koendv/arm_can_tool/Hardware/V1.0/5_3D/enclosure/README.md

3D shell for [arm_can_tool](https://oshwlab.com/koendv/arm_can_tool)

| Model | Print using | Color | Description |
| --- | --- | --- | --- |
| 3DShell_3DShell_PCB1_B.stl | SLA resin 8001 | transparent | 3D Shell, Display side |
| 3DShell_3DShell_PCB1_T.stl | SLA resin 9600 | white | 3D Shell, Component side |
