koendv/arm_can_tool/Hardware/V1.0/5_3D/fixture/README.md

 PCB Assembly Fixture for glueing ZJY154-2828KSWKG03 OLED to ARM CAN TOOL PCB.
 
 This fixture 
 
 - HOLDS the 60x100mm PCB securely in place via press-fit bumps
 - POSITIONS the OLED display accurately for gluing
