koendv/arm_can_tool/doc/pictures/3d_pcb_front.png

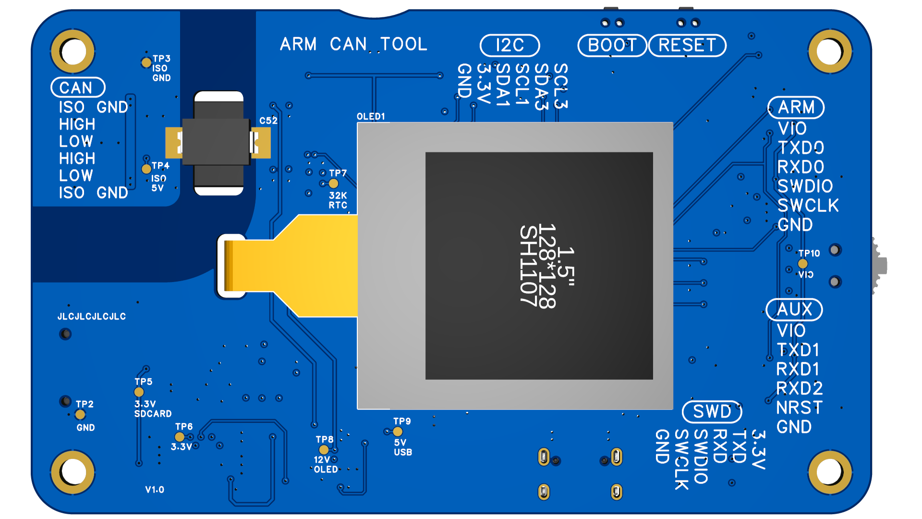
doc/pictures/3d_pcb_front.png
