koendv/arm_can_tool/doc/pictures/back_big.jpg

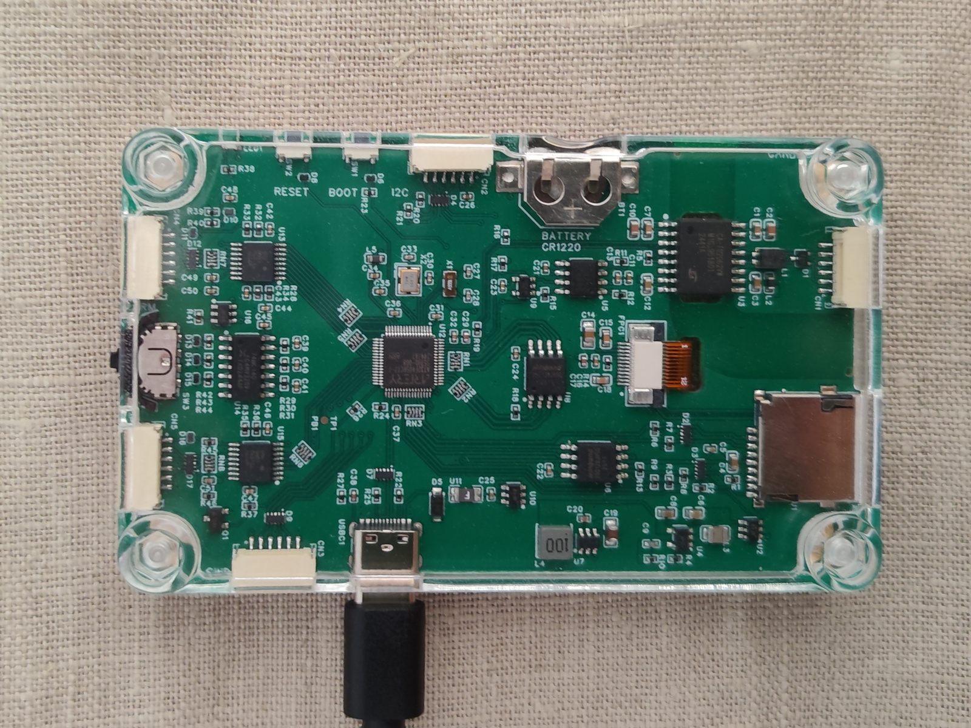
doc/pictures/back_big.jpg
