koendv/arm_can_tool/doc/pictures/handbook.png

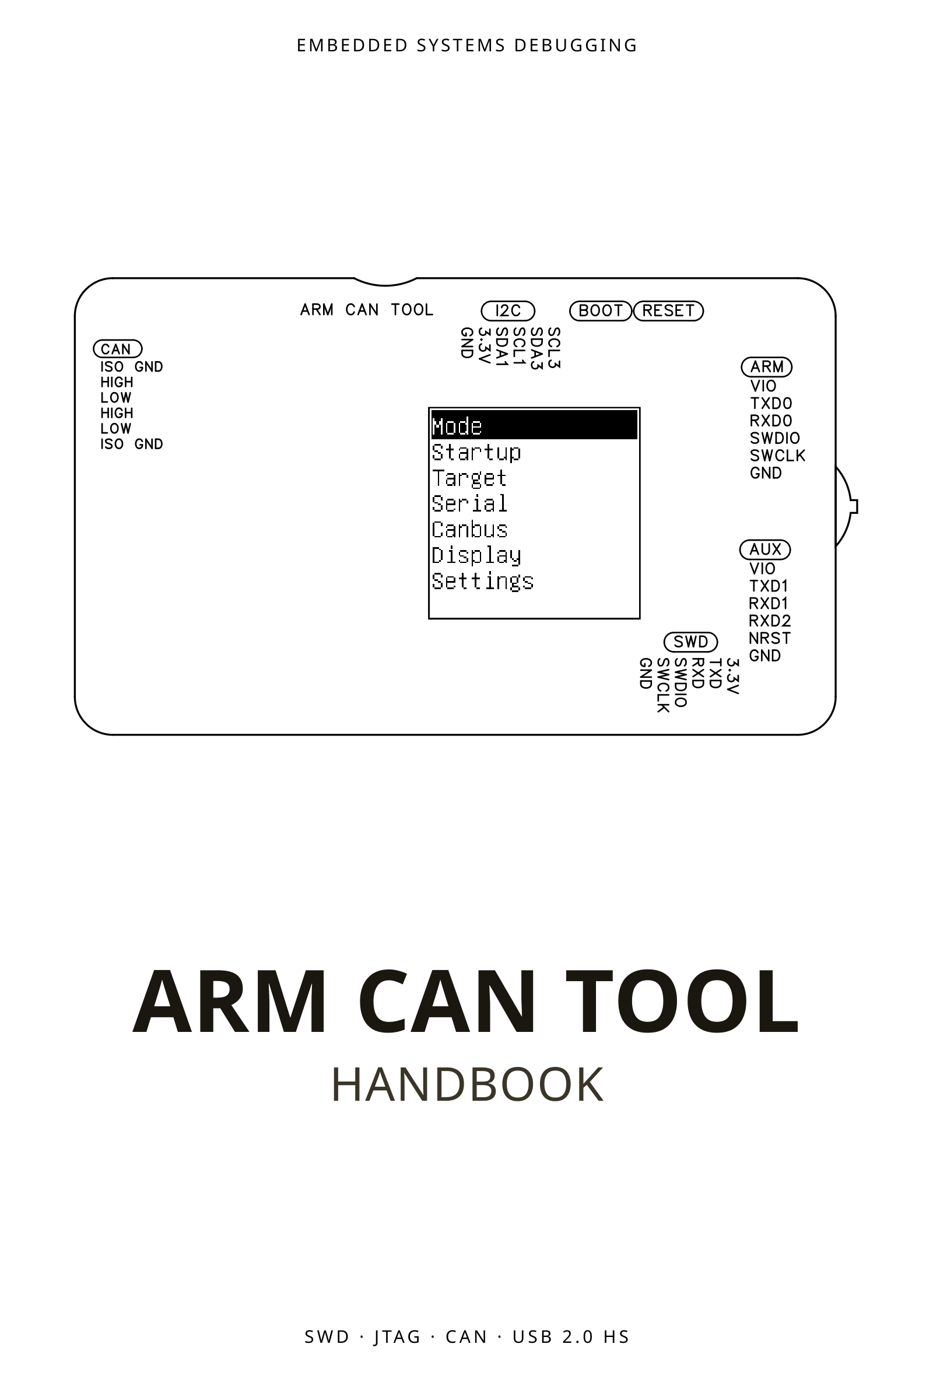
doc/pictures/handbook.png
