koendv/arm_can_tool/doc/pictures/menu_mode.png

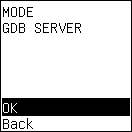
doc/pictures/menu_mode.png
