koendv/arm_can_tool/doc/pictures/oled_zjy.png

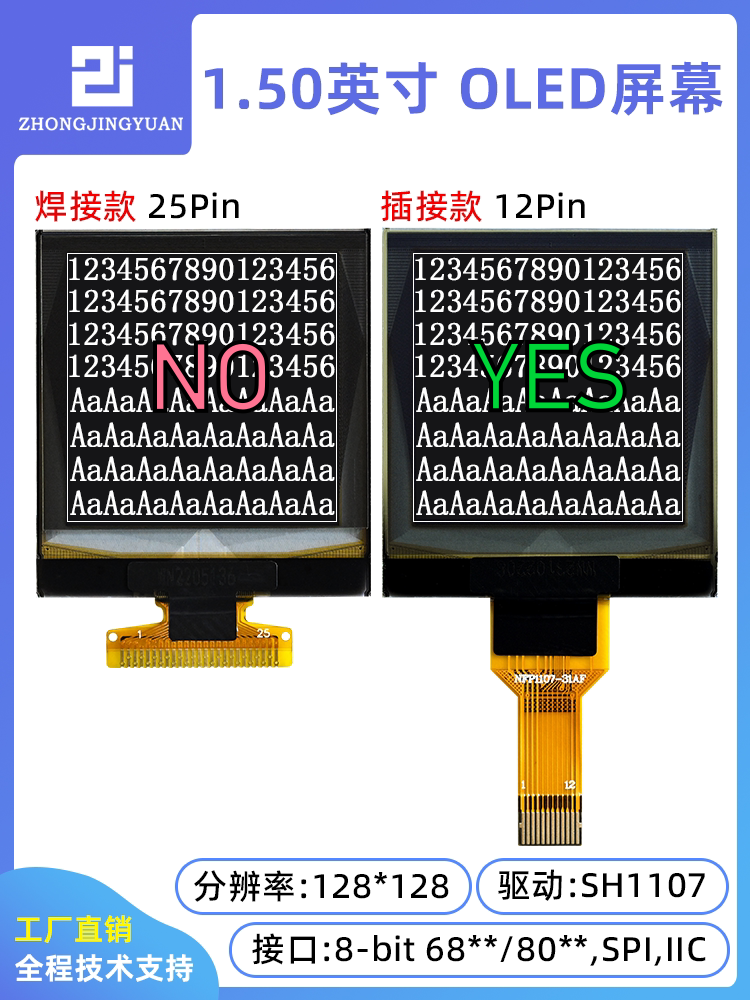
doc/pictures/oled_zjy.png
