koendv/arm_can_tool/doc/pictures/pcb_display_big.jpg

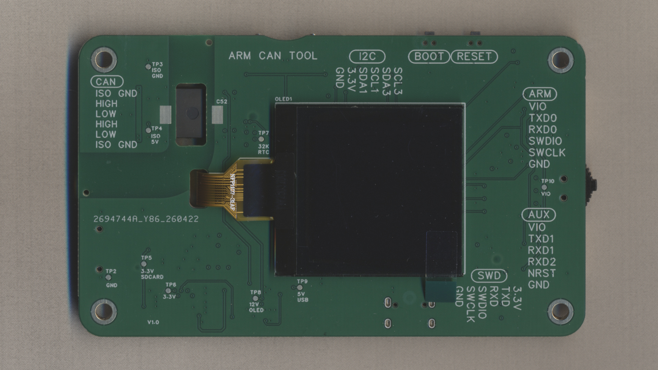
doc/pictures/pcb_display_big.jpg
