koendv/arm_can_tool/doc/pictures/target_cable.jpg

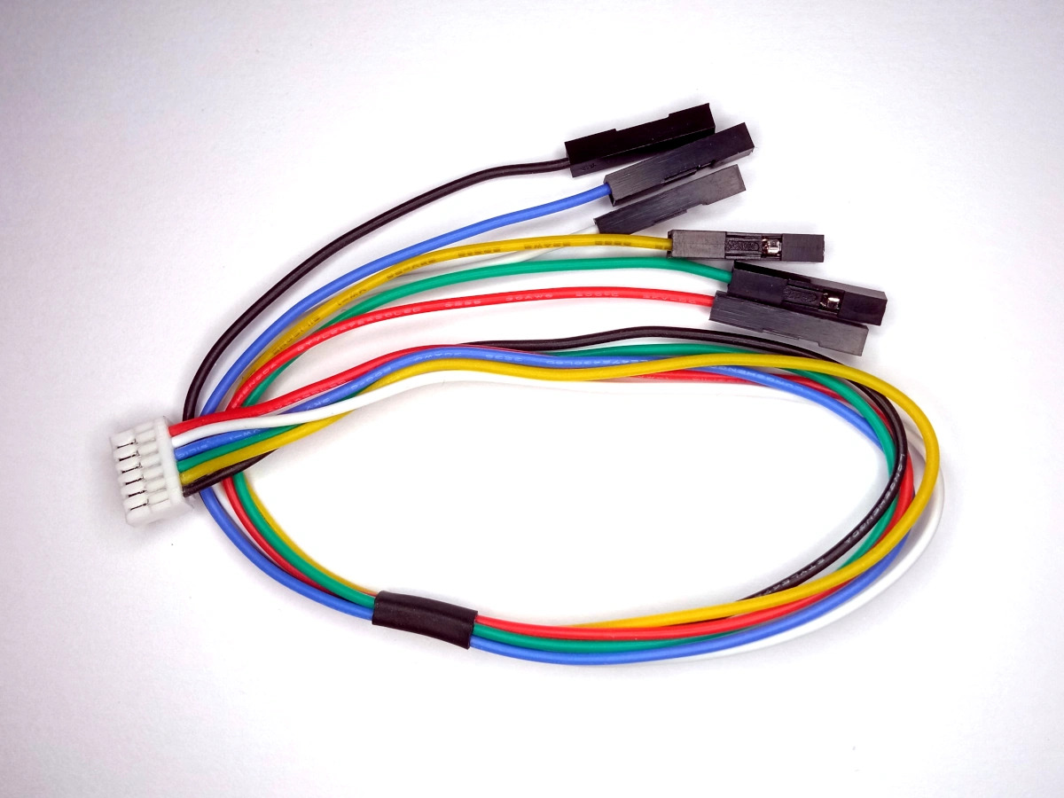
doc/pictures/target_cable.jpg
