koendv/arm_can_tool/Hardware/V1.0/6_DOC/pcb_analysis.yaml

metadata:
  component_count: 174
  net_count: 136
  verbosity_level: 5
  verbosity_description: 'EXHAUSTIVE: + All original BOM fields'
  generation_timestamp: '2026-04-23T06:47:56.703190'
  generator: EasyEDA Parser v1.0
  data_sources:
    bom: 'Bill of Materials: Component specifications, values, manufacturers'
    pickplace: 'Pick & Place: Physical coordinates, rotation, layer for assembly'
    netlist: 'Netlist: Electrical pin-to-pin connectivity'
    schematic: 'Schematic PDF: SCH_Schematic1_2026-04-18.pdf, 3 pages'
  project:
    name: arm_can_tool
    author: koendv
    license: CC0 PUBLIC DOMAIN
    version: '1.0'
    schematic_part_number: JLCPCB-002
    schematic_size: A3
    schematic_pages: 3
    schematic_create_date: '2026-01-16'
    schematic_update_date: '2026-04-17'
    page_titles:
      P1: PROCESSOR AND POWER
      P2: I2C AND SPI
      P3: TARGET AND CAN
  pcb_fab:
    vendor: JLCPCB
    stackup: JLC04161H-7628
    layers: 4
    controlled_impedance: true
    impedance_targets:
      usb_differential_pair: 90_ohm_differential
      single_ended_50ohm: 13_mil_trace
      usb_trace_spacing: 8_mil_space
      usb_trace_width: 10_mil
  design_checklist:
  - item: No silkscreen in CAN bus isolation barrier
    status: required
  - item: DS3231 RTC interrupt on MCU EXTI pin (PC13)
    status: verified
  - item: Target T_SWO/TRACESWO on USART RX
    status: verify_in_firmware
  - item: SD card length and impedance matching
    status: layout_action_required
  - item: USB differential pair length matching and 90-ohm impedance
    status: layout_action_required
  - item: Transmission lines routed over ground plane
    status: layout_action_required
  - item: No solder paste on middle pad of battery holder BT1 (C964818)
    status: assembly_note
  - item: Order number on PCB - specify position
    status: fab_action_required
  mechanical:
    shell_component_side: SLA resin 9600 white
    shell_display_side: SLA resin 8100 transparent
    fasteners: 4x nylon M3 10mm screws and nuts
    mounting_holes: M1 M2 M3 M4 (3.2mm)
  emc_notes:
  - C52 (2.2nF 400VAC Y-capacitor across isolation barrier) DNP by default, EMC debugging
    only
  - L1 ACT1210-510-2P-TL00 is a dual-winding common-mode choke on CAN_HI/CAN_LO
  - L2 GZ1608D601TF is a ferrite bead on CAN_5V_IN supply
  coordinate_system:
    units: millimeters (mm)
    origin: Bottom-left corner of PCB (standard PCB manufacturing coordinates)
    x_axis: Horizontal, increasing to the right
    y_axis: Vertical, increasing upward
    rotation: Degrees, counter-clockwise positive (0° = component oriented as in datasheet)
    placement_reference: Coordinates are from the component center (Mid X, Mid Y)
    estimated_board_size: 65.4mm × 103.1mm
    component_extent: &id001
      min_x_mm: 1.7
      max_x_mm: 57.0
      min_y_mm: 3.9
      max_y_mm: 97.0
      width_mm: 55.4
      height_mm: 93.1
  layer_codes:
    T: Top layer (components on top side of PCB)
    B: Bottom layer (components on bottom side)
  interpretation_notes:
  - Component types (R=resistor, C=capacitor, L=inductor, U=IC, etc.) are inferred
    from designator prefixes
  - Placement coordinates show physical layout - components near each other are functionally
    related
  - Net connections show electrical connectivity - components on same net are electrically
    connected
  - Rotation 0° means component oriented as shown in datasheet, 90° means rotated
    90° counter-clockwise
  - This data comes from EasyEDA Pro exports and preserves all original information
  board_dimensions:
    width_mm: 65.4
    height_mm: 103.1
    estimated_board_size: 65.4mm × 103.1mm
    component_extent: *id001
    note: Dimensions estimated from component placement with 5mm margin
components:
- designator: BT1
  type: battery
  value: MY-1220-03
  footprint: BAT-SMD_MY-1220-03
  comment: MY-1220-03
  manufacturer: MYOUNG(美阳)
  manufacturer_part: MY-1220-03
  supplier_part: C964818
  placement:
    x_mm: 5.08
    y_mm: 59.69
    rotation_deg: 90.0
    layer: T
  pins:
    '1': VBAT
    '2': VBAT
    '3': GND
  bom_data:
    No.: '1'
    Designator: BT1
    Quantity: '1'
    Manufacturer: MYOUNG(美阳)
    Manufacturer Part: MY-1220-03
    Comment: MY-1220-03
    Footprint: BAT-SMD_MY-1220-03
    Mounting Style: SMT
    Supplier Part: C964818
    Datasheet: https://atta.szlcsc.com/upload/public/pdf/source/20201218/C964818_B03812FB908E34364C1125E65C8EBE5C.pdf
  schematic_page: P1
  function_block: RTC backup battery
  schematic_notes:
  - CR1220 coin cell; powers VBAT rail when main supply is absent
  - 'Assembly: no solder paste on middle pad of holder C964818'
- designator: C1
  type: capacitor
  value: 100nF
  footprint: C0603
  comment: 100nF
  manufacturer: YAGEO(国巨)
  manufacturer_part: CC0603KRX7R9BB104
  supplier_part: C14663
  placement:
    x_mm: 12.065
    y_mm: 85.725
    rotation_deg: 180.0
    layer: T
  pins:
    '1': CAN_GND
    '2': CAN_5V_OUT
  bom_data:
    No.: '2'
    Designator: C1,C7,C15,C18
    Quantity: '4'
    Manufacturer: YAGEO(国巨)
    Manufacturer Part: CC0603KRX7R9BB104
    Comment: 100nF
    Footprint: C0603
    Mounting Style: SMT
    Supplier Part: C14663
    Datasheet: https://atta.szlcsc.com/upload/public/pdf/source/20180910/C282072_33301C7F631E79921B82A8DAC6BCC5B3.pdf
  schematic_page: P3
  function_block: CAN transceiver VCC decoupling (3.3V side)
  schematic_notes:
  - 100nF decoupling for U3 VCC pin (3.3V domain)
- designator: C2
  type: capacitor
  value: 10uF
  footprint: C0603
  comment: 10uF
  manufacturer: SAMSUNG(三星)
  manufacturer_part: CL10A106MA8NRNC
  supplier_part: C96446
  placement:
    x_mm: 12.065
    y_mm: 87.63
    rotation_deg: 180.0
    layer: T
  pins:
    '1': CAN_GND
    '2': CAN_5V_OUT
  bom_data:
    No.: '3'
    Designator: C2,C10
    Quantity: '2'
    Manufacturer: SAMSUNG(三星)
    Manufacturer Part: CL10A106MA8NRNC
    Comment: 10uF
    Footprint: C0603
    Mounting Style: SMT
    Supplier Part: C96446
    Datasheet: https://atta.szlcsc.com/upload/public/pdf/source/20160218/1457707763339.pdf
  schematic_page: P3
  function_block: CAN transceiver VCC bulk decoupling (3.3V side)
  schematic_notes:
  - 10uF bulk cap for U3 VCC (3.3V domain)
- designator: C3
  type: capacitor
  value: 1uF
  footprint: C0603
  comment: 1uF
  manufacturer: SAMSUNG(三星)
  manufacturer_part: CL10A105KB8NNNC
  supplier_part: C15849
  placement:
    x_mm: 19.304
    y_mm: 85.725
    rotation_deg: 180.0
    layer: T
  pins:
    '1': CAN_GND
    '2': CAN_5V_IN
  bom_data:
    No.: '4'
    Designator: C3,C12
    Quantity: '2'
    Manufacturer: SAMSUNG(三星)
    Manufacturer Part: CL10A105KB8NNNC
    Comment: 1uF
    Footprint: C0603
    Mounting Style: SMT
    Supplier Part: C15849
    Datasheet: https://atta.szlcsc.com/upload/public/pdf/source/20160218/1457707763339.pdf
  schematic_page: P3
  function_block: CAN transceiver VISO decoupling
  schematic_notes:
  - 1uF decoupling for U3 isolated VISO supply (CAN side)
- designator: C4
  type: capacitor
  value: 4.7uF
  footprint: C0603
  comment: 4.7uF
  manufacturer: SAMSUNG(三星)
  manufacturer_part: CL10A475KO8NNNC
  supplier_part: C19666
  placement:
    x_mm: 43.81
    y_mm: 82.677
    rotation_deg: 180.0
    layer: T
  pins:
    '1': GND
    '2': VSD
  bom_data:
    No.: '5'
    Designator: C4,C8
    Quantity: '2'
    Manufacturer: SAMSUNG(三星)
    Manufacturer Part: CL10A475KO8NNNC
    Comment: 4.7uF
    Footprint: C0603
    Mounting Style: SMT
    Supplier Part: C19666
    Datasheet: https://item.szlcsc.com/datasheet/CL10A475KO8NNNC/20375.html
  schematic_page: P2
  function_block: SD card VSD bulk decoupling
  schematic_notes:
  - 4.7uF bulk decoupling on VSD rail for SD card power switch U2
- designator: C5
  type: capacitor
  value: 100nF
  footprint: C0402
  comment: 100nF
  manufacturer: SAMSUNG(三星)
  manufacturer_part: CL05B104KO5NNNC
  supplier_part: C1525
  placement:
    x_mm: 42.037
    y_mm: 79.629
    rotation_deg: 270.0
    layer: T
  pins:
    '1': VSD
    '2': GND
  bom_data:
    No.: '6'
    Designator: C5,C13,C16,C22,C23,C24,C31,C32,C35,C36,C37,C42,C43,C44,C45,C46,C47,C48,C50,C51
    Quantity: '20'
    Manufacturer: SAMSUNG(三星)
    Manufacturer Part: CL05B104KO5NNNC
    Comment: 100nF
    Footprint: C0402
    Mounting Style: SMT
    Supplier Part: C1525
    Datasheet: https://atta.szlcsc.com/upload/public/pdf/source/20160218/1457707763339.pdf
  schematic_page: P2
  function_block: SD card VSD decoupling
  schematic_notes:
  - 100nF decoupling on VSD rail
- designator: C6
  type: capacitor
  value: 22uF
  footprint: C0603
  comment: 22uF
  manufacturer: SAMSUNG(三星)
  manufacturer_part: CL10A226MQ8NRNC
  supplier_part: C59461
  placement:
    x_mm: 50.8
    y_mm: 77.343
    rotation_deg: 90.0
    layer: T
  pins:
    '1': GND
    '2': 3.3V
  bom_data:
    No.: '7'
    Designator: C6
    Quantity: '1'
    Manufacturer: SAMSUNG(三星)
    Manufacturer Part: CL10A226MQ8NRNC
    Comment: 22uF
    Footprint: C0603
    Mounting Style: SMT
    Supplier Part: C59461
    Datasheet: https://atta.szlcsc.com/upload/public/pdf/source/20160218/1457707763339.pdf
  schematic_page: P1
  function_block: 3.3V bulk decoupling (CPU)
  schematic_notes:
  - 22uF bulk cap on 3.3V rail near MCU U12
- designator: C7
  type: capacitor
  value: 100nF
  footprint: C0603
  comment: 100nF
  manufacturer: YAGEO(国巨)
  manufacturer_part: CC0603KRX7R9BB104
  supplier_part: C14663
  placement:
    x_mm: 12.065
    y_mm: 70.739
    rotation_deg: 180.0
    layer: T
  pins:
    '1': GND
    '2': 5V
  bom_data:
    No.: '2'
    Designator: C1,C7,C15,C18
    Quantity: '4'
    Manufacturer: YAGEO(国巨)
    Manufacturer Part: CC0603KRX7R9BB104
    Comment: 100nF
    Footprint: C0603
    Mounting Style: SMT
    Supplier Part: C14663
    Datasheet: https://atta.szlcsc.com/upload/public/pdf/source/20180910/C282072_33301C7F631E79921B82A8DAC6BCC5B3.pdf
  schematic_page: P3
  function_block: CAN transceiver 5V decoupling
  schematic_notes:
  - 100nF decoupling for U3 VCC 5V supply
- designator: C8
  type: capacitor
  value: 4.7uF
  footprint: C0603
  comment: 4.7uF
  manufacturer: SAMSUNG(三星)
  manufacturer_part: CL10A475KO8NNNC
  supplier_part: C19666
  placement:
    x_mm: 50.8
    y_mm: 73.533
    rotation_deg: 270.0
    layer: T
  pins:
    '1': GND
    '2': 5V
  bom_data:
    No.: '5'
    Designator: C4,C8
    Quantity: '2'
    Manufacturer: SAMSUNG(三星)
    Manufacturer Part: CL10A475KO8NNNC
    Comment: 4.7uF
    Footprint: C0603
    Mounting Style: SMT
    Supplier Part: C19666
    Datasheet: https://item.szlcsc.com/datasheet/CL10A475KO8NNNC/20375.html
  schematic_page: P1
  function_block: USB VBUS bulk decoupling
  schematic_notes:
  - 4.7uF bulk decoupling on 5V/VBUS rail near USB-C connector
- designator: C9
  type: capacitor
  value: 22pF
  footprint: C0402
  comment: 22pF
  manufacturer: FH(风华)
  manufacturer_part: 0402CG220J500NT
  supplier_part: C1555
  placement:
    x_mm: 54.991
    y_mm: 71.501
    rotation_deg: 270.0
    layer: T
  pins:
    '1': VFB
    '2': 3.3V
  bom_data:
    No.: '8'
    Designator: C9
    Quantity: '1'
    Manufacturer: FH(风华)
    Manufacturer Part: 0402CG220J500NT
    Comment: 22pF
    Footprint: C0402
    Mounting Style: SMT
    Supplier Part: C1555
  schematic_page: P1
  function_block: Buck converter VFB feed-forward capacitor
  schematic_notes:
  - 22pF feed-forward cap across upper feedback resistor R10 for TLV62569 U4
  - Improves phase margin of 3.3V buck converter loop
- designator: C10
  type: capacitor
  value: 10uF
  footprint: C0603
  comment: 10uF
  manufacturer: SAMSUNG(三星)
  manufacturer_part: CL10A106MA8NRNC
  supplier_part: C96446
  placement:
    x_mm: 12.065
    y_mm: 68.834
    rotation_deg: 180.0
    layer: T
  pins:
    '1': GND
    '2': 5V
  bom_data:
    No.: '3'
    Designator: C2,C10
    Quantity: '2'
    Manufacturer: SAMSUNG(三星)
    Manufacturer Part: CL10A106MA8NRNC
    Comment: 10uF
    Footprint: C0603
    Mounting Style: SMT
    Supplier Part: C96446
    Datasheet: https://atta.szlcsc.com/upload/public/pdf/source/20160218/1457707763339.pdf
  schematic_page: P3
  function_block: CAN transceiver VISO bulk decoupling
  schematic_notes:
  - 10uF bulk cap on U3 isolated VISO rail (CAN side)
- designator: C11
  type: capacitor
  value: 1uF
  footprint: C0402
  comment: 1uF
  manufacturer: SAMSUNG(三星)
  manufacturer_part: CL05A105KA5NQNC
  supplier_part: C52923
  placement:
    x_mm: 18.796
    y_mm: 68.199
    rotation_deg: 0.0
    layer: T
  pins:
    '1': GND
    '2': 3.3V
  bom_data:
    No.: '9'
    Designator: C11,C21,C25,C26,C34,C39,C40,C41,C49
    Quantity: '9'
    Manufacturer: SAMSUNG(三星)
    Manufacturer Part: CL05A105KA5NQNC
    Comment: 1uF
    Footprint: C0402
    Mounting Style: SMT
    Supplier Part: C52923
    Datasheet: https://atta.szlcsc.com/upload/public/pdf/source/20160218/1457707763339.pdf
  schematic_page: P2
  function_block: 3.3V decoupling (I2C/SPI area)
  schematic_notes:
  - 1uF local 3.3V decoupling near I2C/SPI peripherals
- designator: C12
  type: capacitor
  value: 1uF
  footprint: C0603
  comment: 1uF
  manufacturer: SAMSUNG(三星)
  manufacturer_part: CL10A105KB8NNNC
  supplier_part: C15849
  placement:
    x_mm: 19.685
    y_mm: 70.739
    rotation_deg: 180.0
    layer: T
  pins:
    '1': GND
    '2': 3.3V
  bom_data:
    No.: '4'
    Designator: C3,C12
    Quantity: '2'
    Manufacturer: SAMSUNG(三星)
    Manufacturer Part: CL10A105KB8NNNC
    Comment: 1uF
    Footprint: C0603
    Mounting Style: SMT
    Supplier Part: C15849
    Datasheet: https://atta.szlcsc.com/upload/public/pdf/source/20160218/1457707763339.pdf
  schematic_page: P3
  function_block: CAN transceiver VISO decoupling
  schematic_notes:
  - 1uF decoupling on U3 isolated VISO supply
- designator: C13
  type: capacitor
  value: 100nF
  footprint: C0402
  comment: 100nF
  manufacturer: SAMSUNG(三星)
  manufacturer_part: CL05B104KO5NNNC
  supplier_part: C1525
  placement:
    x_mm: 18.796
    y_mm: 66.675
    rotation_deg: 0.0
    layer: T
  pins:
    '1': GND
    '2': 3.3V
  bom_data:
    No.: '6'
    Designator: C5,C13,C16,C22,C23,C24,C31,C32,C35,C36,C37,C42,C43,C44,C45,C46,C47,C48,C50,C51
    Quantity: '20'
    Manufacturer: SAMSUNG(三星)
    Manufacturer Part: CL05B104KO5NNNC
    Comment: 100nF
    Footprint: C0402
    Mounting Style: SMT
    Supplier Part: C1525
    Datasheet: https://atta.szlcsc.com/upload/public/pdf/source/20160218/1457707763339.pdf
  schematic_page: P2
  function_block: RTC 3.3V decoupling
  schematic_notes:
  - 100nF decoupling for RTC IC U5
- designator: C14
  type: capacitor
  value: 2.2uF
  footprint: C0805
  comment: 2.2uF
  manufacturer: SAMSUNG(三星)
  manufacturer_part: CL21A225KBQNNNE
  supplier_part: C377773
  placement:
    x_mm: 26.543
    y_mm: 62.738
    rotation_deg: 0.0
    layer: T
  pins:
    '1': GND
    '2': VCOMH
  bom_data:
    No.: '10'
    Designator: C14
    Quantity: '1'
    Manufacturer: SAMSUNG(三星)
    Manufacturer Part: CL21A225KBQNNNE
    Comment: 2.2uF
    Footprint: C0805
    Mounting Style: SMT
    Supplier Part: C377773
    Datasheet: https://atta.szlcsc.com/upload/public/pdf/source/20160218/1457707763339.pdf
  schematic_page: P2
  function_block: Display VCOMH storage capacitor
  schematic_notes:
  - 2.2uF VCOMH cap for OLED display via FPC1
  - 50V rated for 12V supply domain
- designator: C15
  type: capacitor
  value: 100nF
  footprint: C0603
  comment: 100nF
  manufacturer: YAGEO(国巨)
  manufacturer_part: CC0603KRX7R9BB104
  supplier_part: C14663
  placement:
    x_mm: 27.051
    y_mm: 65.151
    rotation_deg: 0.0
    layer: T
  pins:
    '1': GND
    '2': 12V
  bom_data:
    No.: '2'
    Designator: C1,C7,C15,C18
    Quantity: '4'
    Manufacturer: YAGEO(国巨)
    Manufacturer Part: CC0603KRX7R9BB104
    Comment: 100nF
    Footprint: C0603
    Mounting Style: SMT
    Supplier Part: C14663
    Datasheet: https://atta.szlcsc.com/upload/public/pdf/source/20180910/C282072_33301C7F631E79921B82A8DAC6BCC5B3.pdf
  schematic_page: P2
  function_block: 12V boost output decoupling
  schematic_notes:
  - 100nF output decoupling for 12V boost U7; 50V rated
- designator: C16
  type: capacitor
  value: 100nF
  footprint: C0402
  comment: 100nF
  manufacturer: SAMSUNG(三星)
  manufacturer_part: CL05B104KO5NNNC
  supplier_part: C1525
  placement:
    x_mm: 30.226
    y_mm: 63.754
    rotation_deg: 180.0
    layer: T
  pins:
    '1': GND
    '2': 3.3V
  bom_data:
    No.: '6'
    Designator: C5,C13,C16,C22,C23,C24,C31,C32,C35,C36,C37,C42,C43,C44,C45,C46,C47,C48,C50,C51
    Quantity: '20'
    Manufacturer: SAMSUNG(三星)
    Manufacturer Part: CL05B104KO5NNNC
    Comment: 100nF
    Footprint: C0402
    Mounting Style: SMT
    Supplier Part: C1525
    Datasheet: https://atta.szlcsc.com/upload/public/pdf/source/20160218/1457707763339.pdf
  schematic_page: P2
  function_block: 12V domain decoupling
  schematic_notes:
  - 100nF decoupling on 12V rail near display FPC1
- designator: C17
  type: capacitor
  value: 4.7uF
  footprint: C0402
  comment: 4.7uF
  manufacturer: SAMSUNG(三星)
  manufacturer_part: CL05A475MP5NRNC
  supplier_part: C23733
  placement:
    x_mm: 30.226
    y_mm: 62.103
    rotation_deg: 180.0
    layer: T
  pins:
    '1': GND
    '2': 3.3V
  bom_data:
    No.: '11'
    Designator: C17,C20,C29
    Quantity: '3'
    Manufacturer: SAMSUNG(三星)
    Manufacturer Part: CL05A475MP5NRNC
    Comment: 4.7uF
    Footprint: C0402
    Mounting Style: SMT
    Supplier Part: C23733
    Datasheet: https://atta.szlcsc.com/upload/public/pdf/source/20160218/1457707763339.pdf
  schematic_page: P2
  function_block: 12V domain bulk decoupling
  schematic_notes:
  - 4.7uF bulk decoupling on 12V rail near display FPC1
- designator: C18
  type: capacitor
  value: 100nF
  footprint: C0603
  comment: 100nF
  manufacturer: YAGEO(国巨)
  manufacturer_part: CC0603KRX7R9BB104
  supplier_part: C14663
  placement:
    x_mm: 32.766
    y_mm: 64.516
    rotation_deg: 90.0
    layer: T
  pins:
    '1': GND
    '2': 12V
  bom_data:
    No.: '2'
    Designator: C1,C7,C15,C18
    Quantity: '4'
    Manufacturer: YAGEO(国巨)
    Manufacturer Part: CC0603KRX7R9BB104
    Comment: 100nF
    Footprint: C0603
    Mounting Style: SMT
    Supplier Part: C14663
    Datasheet: https://atta.szlcsc.com/upload/public/pdf/source/20180910/C282072_33301C7F631E79921B82A8DAC6BCC5B3.pdf
  schematic_page: P2
  function_block: 12V boost output decoupling
  schematic_notes:
  - 100nF output decoupling for U7 12V boost; 50V rated
- designator: C19
  type: capacitor
  value: 10uF
  footprint: C0805
  comment: 10uF
  manufacturer: muRata(村田)
  manufacturer_part: GRM21BR61H106KE43L
  supplier_part: C440198
  placement:
    x_mm: 53.467
    y_mm: 65.913
    rotation_deg: 180.0
    layer: T
  pins:
    '1': GND
    '2': 12V
  bom_data:
    No.: '12'
    Designator: C19
    Quantity: '1'
    Manufacturer: muRata(村田)
    Manufacturer Part: GRM21BR61H106KE43L
    Comment: 10uF
    Footprint: C0805
    Mounting Style: SMT
    Supplier Part: C440198
    Datasheet: https://atta.szlcsc.com/upload/public/pdf/source/20230811/95AAE0C9AF55EDC31B7A4D8B733F534E.pdf
  schematic_page: P2
  function_block: 12V boost output bulk capacitor
  schematic_notes:
  - 10uF bulk output cap for 12V boost U7; 50V rated (Murata)
- designator: C20
  type: capacitor
  value: 4.7uF
  footprint: C0402
  comment: 4.7uF
  manufacturer: SAMSUNG(三星)
  manufacturer_part: CL05A475MP5NRNC
  supplier_part: C23733
  placement:
    x_mm: 51.562
    y_mm: 62.23
    rotation_deg: 270.0
    layer: T
  pins:
    '1': GND
    '2': 5V
  bom_data:
    No.: '11'
    Designator: C17,C20,C29
    Quantity: '3'
    Manufacturer: SAMSUNG(三星)
    Manufacturer Part: CL05A475MP5NRNC
    Comment: 4.7uF
    Footprint: C0402
    Mounting Style: SMT
    Supplier Part: C23733
    Datasheet: https://atta.szlcsc.com/upload/public/pdf/source/20160218/1457707763339.pdf
  schematic_page: P2
  function_block: 5V decoupling (boost converter input)
  schematic_notes:
  - 4.7uF input decoupling for 12V boost U7, on 5V rail
- designator: C21
  type: capacitor
  value: 1uF
  footprint: C0402
  comment: 1uF
  manufacturer: SAMSUNG(三星)
  manufacturer_part: CL05A105KA5NQNC
  supplier_part: C52923
  placement:
    x_mm: 17.526
    y_mm: 56.769
    rotation_deg: 0.0
    layer: T
  pins:
    '1': GND
    '2': VBAT
  bom_data:
    No.: '9'
    Designator: C11,C21,C25,C26,C34,C39,C40,C41,C49
    Quantity: '9'
    Manufacturer: SAMSUNG(三星)
    Manufacturer Part: CL05A105KA5NQNC
    Comment: 1uF
    Footprint: C0402
    Mounting Style: SMT
    Supplier Part: C52923
    Datasheet: https://atta.szlcsc.com/upload/public/pdf/source/20160218/1457707763339.pdf
  schematic_page: P2
  function_block: VBAT decoupling
  schematic_notes:
  - 1uF decoupling on VBAT rail for RTC backup battery BT1
- designator: C22
  type: capacitor
  value: 100nF
  footprint: C0402
  comment: 100nF
  manufacturer: SAMSUNG(三星)
  manufacturer_part: CL05B104KO5NNNC
  supplier_part: C1525
  placement:
    x_mm: 45.085
    y_mm: 57.404
    rotation_deg: 180.0
    layer: T
  pins:
    '1': 3.3V
    '2': GND
  bom_data:
    No.: '6'
    Designator: C5,C13,C16,C22,C23,C24,C31,C32,C35,C36,C37,C42,C43,C44,C45,C46,C47,C48,C50,C51
    Quantity: '20'
    Manufacturer: SAMSUNG(三星)
    Manufacturer Part: CL05B104KO5NNNC
    Comment: 100nF
    Footprint: C0402
    Mounting Style: SMT
    Supplier Part: C1525
    Datasheet: https://atta.szlcsc.com/upload/public/pdf/source/20160218/1457707763339.pdf
  schematic_page: P3
  function_block: VIO decoupling (target interface)
  schematic_notes:
  - 100nF decoupling on VIO rail for target voltage domain
- designator: C23
  type: capacitor
  value: 100nF
  footprint: C0402
  comment: 100nF
  manufacturer: SAMSUNG(三星)
  manufacturer_part: CL05B104KO5NNNC
  supplier_part: C1525
  placement:
    x_mm: 20.066
    y_mm: 50.927
    rotation_deg: 180.0
    layer: T
  pins:
    '1': GND
    '2': 3.3V
  bom_data:
    No.: '6'
    Designator: C5,C13,C16,C22,C23,C24,C31,C32,C35,C36,C37,C42,C43,C44,C45,C46,C47,C48,C50,C51
    Quantity: '20'
    Manufacturer: SAMSUNG(三星)
    Manufacturer Part: CL05B104KO5NNNC
    Comment: 100nF
    Footprint: C0402
    Mounting Style: SMT
    Supplier Part: C1525
    Datasheet: https://atta.szlcsc.com/upload/public/pdf/source/20160218/1457707763339.pdf
  schematic_page: P2
  function_block: EEPROM 3.3V decoupling
  schematic_notes:
  - 100nF decoupling for EEPROM U9
- designator: C24
  type: capacitor
  value: 100nF
  footprint: C0402
  comment: 100nF
  manufacturer: SAMSUNG(三星)
  manufacturer_part: CL05B104KO5NNNC
  supplier_part: C1525
  placement:
    x_mm: 29.286
    y_mm: 52.832
    rotation_deg: 0.0
    layer: T
  pins:
    '1': 3.3V
    '2': GND
  bom_data:
    No.: '6'
    Designator: C5,C13,C16,C22,C23,C24,C31,C32,C35,C36,C37,C42,C43,C44,C45,C46,C47,C48,C50,C51
    Quantity: '20'
    Manufacturer: SAMSUNG(三星)
    Manufacturer Part: CL05B104KO5NNNC
    Comment: 100nF
    Footprint: C0402
    Mounting Style: SMT
    Supplier Part: C1525
    Datasheet: https://atta.szlcsc.com/upload/public/pdf/source/20160218/1457707763339.pdf
  schematic_page: P1
  function_block: QSPI flash 3.3V decoupling
  schematic_notes:
  - 100nF decoupling for QSPI flash U8
- designator: C25
  type: capacitor
  value: 1uF
  footprint: C0402
  comment: 1uF
  manufacturer: SAMSUNG(三星)
  manufacturer_part: CL05A105KA5NQNC
  supplier_part: C52923
  placement:
    x_mm: 48.387
    y_mm: 49.53
    rotation_deg: 0.0
    layer: T
  pins:
    '1': GND
    '2': VBUS
  bom_data:
    No.: '9'
    Designator: C11,C21,C25,C26,C34,C39,C40,C41,C49
    Quantity: '9'
    Manufacturer: SAMSUNG(三星)
    Manufacturer Part: CL05A105KA5NQNC
    Comment: 1uF
    Footprint: C0402
    Mounting Style: SMT
    Supplier Part: C52923
    Datasheet: https://atta.szlcsc.com/upload/public/pdf/source/20160218/1457707763339.pdf
  schematic_page: P1
  function_block: USB VBUS decoupling
  schematic_notes:
  - 1uF decoupling on VBUS rail; 25V rated
- designator: C26
  type: capacitor
  value: 1uF
  footprint: C0402
  comment: 1uF
  manufacturer: SAMSUNG(三星)
  manufacturer_part: CL05A105KA5NQNC
  supplier_part: C52923
  placement:
    x_mm: 7.874
    y_mm: 45.974
    rotation_deg: 270.0
    layer: T
  pins:
    '1': GND
    '2': 3.3V
  bom_data:
    No.: '9'
    Designator: C11,C21,C25,C26,C34,C39,C40,C41,C49
    Quantity: '9'
    Manufacturer: SAMSUNG(三星)
    Manufacturer Part: CL05A105KA5NQNC
    Comment: 1uF
    Footprint: C0402
    Mounting Style: SMT
    Supplier Part: C52923
    Datasheet: https://atta.szlcsc.com/upload/public/pdf/source/20160218/1457707763339.pdf
  schematic_page: P2
  function_block: 3.3V decoupling (SPI flash area)
  schematic_notes:
  - 1uF local decoupling near SPI flash U6
- designator: C27
  type: capacitor
  value: 18pF
  footprint: C0402
  comment: 18pF
  manufacturer: FH(风华)
  manufacturer_part: 0402CG180J500NT
  supplier_part: C1549
  placement:
    x_mm: 18.161
    y_mm: 46.228
    rotation_deg: 180.0
    layer: T
  pins:
    '1': GND
    '2': OSC32_OUT
  bom_data:
    No.: '13'
    Designator: C27,C28
    Quantity: '2'
    Manufacturer: FH(风华)
    Manufacturer Part: 0402CG180J500NT
    Comment: 18pF
    Footprint: C0402
    Mounting Style: SMT
    Supplier Part: C1549
    Datasheet: https://atta.szlcsc.com/upload/public/pdf/source/20200305/C486355_26A10D38EF8C2A5C37091D0039909270.pdf
  schematic_page: P1
  function_block: RTC crystal load capacitor (OSC32_OUT)
  schematic_notes:
  - 18pF load cap for 32.768kHz crystal X1, OSC32_OUT pin
- designator: C28
  type: capacitor
  value: 18pF
  footprint: C0402
  comment: 18pF
  manufacturer: FH(风华)
  manufacturer_part: 0402CG180J500NT
  supplier_part: C1549
  placement:
    x_mm: 21.463
    y_mm: 46.228
    rotation_deg: 0.0
    layer: T
  pins:
    '1': GND
    '2': OSC32_IN
  bom_data:
    No.: '13'
    Designator: C27,C28
    Quantity: '2'
    Manufacturer: FH(风华)
    Manufacturer Part: 0402CG180J500NT
    Comment: 18pF
    Footprint: C0402
    Mounting Style: SMT
    Supplier Part: C1549
    Datasheet: https://atta.szlcsc.com/upload/public/pdf/source/20200305/C486355_26A10D38EF8C2A5C37091D0039909270.pdf
  schematic_page: P1
  function_block: RTC crystal load capacitor (OSC32_IN)
  schematic_notes:
  - 18pF load cap for 32.768kHz crystal X1, OSC32_IN pin
- designator: C29
  type: capacitor
  value: 4.7uF
  footprint: C0402
  comment: 4.7uF
  manufacturer: SAMSUNG(三星)
  manufacturer_part: CL05A475MP5NRNC
  supplier_part: C23733
  placement:
    x_mm: 27.051
    y_mm: 45.974
    rotation_deg: 180.0
    layer: T
  pins:
    '1': GND
    '2': 3.3V
  bom_data:
    No.: '11'
    Designator: C17,C20,C29
    Quantity: '3'
    Manufacturer: SAMSUNG(三星)
    Manufacturer Part: CL05A475MP5NRNC
    Comment: 4.7uF
    Footprint: C0402
    Mounting Style: SMT
    Supplier Part: C23733
    Datasheet: https://atta.szlcsc.com/upload/public/pdf/source/20160218/1457707763339.pdf
  schematic_page: P1
  function_block: 3.3V bulk decoupling (CPU)
  schematic_notes:
  - 4.7uF bulk decoupling on 3.3V rail near MCU
- designator: C30
  type: capacitor
  value: 15pF
  footprint: C0402
  comment: 15pF
  manufacturer: FH(风华)
  manufacturer_part: 0402CG150J500NT
  supplier_part: C1548
  placement:
    x_mm: 19.05
    y_mm: 40.894
    rotation_deg: 180.0
    layer: T
  pins:
    '1': OSC_IN
    '2': GND
  bom_data:
    No.: '14'
    Designator: C30,C33
    Quantity: '2'
    Manufacturer: FH(风华)
    Manufacturer Part: 0402CG150J500NT
    Comment: 15pF
    Footprint: C0402
    Mounting Style: SMT
    Supplier Part: C1548
    Datasheet: https://atta.szlcsc.com/upload/public/pdf/source/20200305/C486355_26A10D38EF8C2A5C37091D0039909270.pdf
  schematic_page: P1
  function_block: HSE crystal load capacitor (OSC_IN)
  schematic_notes:
  - 15pF load cap for 12MHz crystal X2, OSC_IN pin
  - 15pF chosen to target 12pF crystal spec with PCB stray capacitance
- designator: C31
  type: capacitor
  value: 100nF
  footprint: C0402
  comment: 100nF
  manufacturer: SAMSUNG(三星)
  manufacturer_part: CL05B104KO5NNNC
  supplier_part: C1525
  placement:
    x_mm: 24.257
    y_mm: 41.91
    rotation_deg: 270.0
    layer: T
  pins:
    '1': GND
    '2': 3.3V
  bom_data:
    No.: '6'
    Designator: C5,C13,C16,C22,C23,C24,C31,C32,C35,C36,C37,C42,C43,C44,C45,C46,C47,C48,C50,C51
    Quantity: '20'
    Manufacturer: SAMSUNG(三星)
    Manufacturer Part: CL05B104KO5NNNC
    Comment: 100nF
    Footprint: C0402
    Mounting Style: SMT
    Supplier Part: C1525
    Datasheet: https://atta.szlcsc.com/upload/public/pdf/source/20160218/1457707763339.pdf
  schematic_page: P1
  function_block: 3.3V decoupling (CPU)
  schematic_notes:
  - 100nF decoupling on 3.3V rail near MCU U12
- designator: C32
  type: capacitor
  value: 100nF
  footprint: C0402
  comment: 100nF
  manufacturer: SAMSUNG(三星)
  manufacturer_part: CL05B104KO5NNNC
  supplier_part: C1525
  placement:
    x_mm: 27.051
    y_mm: 44.323
    rotation_deg: 180.0
    layer: T
  pins:
    '1': GND
    '2': 3.3V
  bom_data:
    No.: '6'
    Designator: C5,C13,C16,C22,C23,C24,C31,C32,C35,C36,C37,C42,C43,C44,C45,C46,C47,C48,C50,C51
    Quantity: '20'
    Manufacturer: SAMSUNG(三星)
    Manufacturer Part: CL05B104KO5NNNC
    Comment: 100nF
    Footprint: C0402
    Mounting Style: SMT
    Supplier Part: C1525
    Datasheet: https://atta.szlcsc.com/upload/public/pdf/source/20160218/1457707763339.pdf
  schematic_page: P1
  function_block: BOOT0 noise filter
  schematic_notes:
  - 100nF noise filter on BOOT0 net
- designator: C33
  type: capacitor
  value: 15pF
  footprint: C0402
  comment: 15pF
  manufacturer: FH(风华)
  manufacturer_part: 0402CG150J500NT
  supplier_part: C1548
  placement:
    x_mm: 16.256
    y_mm: 38.1
    rotation_deg: 270.0
    layer: T
  pins:
    '1': GND
    '2': OSC_OUT
  bom_data:
    No.: '14'
    Designator: C30,C33
    Quantity: '2'
    Manufacturer: FH(风华)
    Manufacturer Part: 0402CG150J500NT
    Comment: 15pF
    Footprint: C0402
    Mounting Style: SMT
    Supplier Part: C1548
    Datasheet: https://atta.szlcsc.com/upload/public/pdf/source/20200305/C486355_26A10D38EF8C2A5C37091D0039909270.pdf
  schematic_page: P1
  function_block: HSE crystal load capacitor (OSC_OUT)
  schematic_notes:
  - 15pF load cap for 12MHz crystal X2, OSC_OUT pin
  - 15pF chosen to target 12pF crystal spec with PCB stray capacitance
- designator: C34
  type: capacitor
  value: 1uF
  footprint: C0402
  comment: 1uF
  manufacturer: SAMSUNG(三星)
  manufacturer_part: CL05A105KA5NQNC
  supplier_part: C52923
  placement:
    x_mm: 18.796
    y_mm: 33.401
    rotation_deg: 270.0
    layer: T
  pins:
    '1': GND
    '2': 3.3V_ANA
  bom_data:
    No.: '9'
    Designator: C11,C21,C25,C26,C34,C39,C40,C41,C49
    Quantity: '9'
    Manufacturer: SAMSUNG(三星)
    Manufacturer Part: CL05A105KA5NQNC
    Comment: 1uF
    Footprint: C0402
    Mounting Style: SMT
    Supplier Part: C52923
    Datasheet: https://atta.szlcsc.com/upload/public/pdf/source/20160218/1457707763339.pdf
  schematic_page: P1
  function_block: MCU VDDA decoupling
  schematic_notes:
  - 1uF decoupling on VDDA (analog supply) for MCU U12
- designator: C35
  type: capacitor
  value: 100nF
  footprint: C0402
  comment: 100nF
  manufacturer: SAMSUNG(三星)
  manufacturer_part: CL05B104KO5NNNC
  supplier_part: C1525
  placement:
    x_mm: 20.955
    y_mm: 34.163
    rotation_deg: 90.0
    layer: T
  pins:
    '1': GND
    '2': RST
  bom_data:
    No.: '6'
    Designator: C5,C13,C16,C22,C23,C24,C31,C32,C35,C36,C37,C42,C43,C44,C45,C46,C47,C48,C50,C51
    Quantity: '20'
    Manufacturer: SAMSUNG(三星)
    Manufacturer Part: CL05B104KO5NNNC
    Comment: 100nF
    Footprint: C0402
    Mounting Style: SMT
    Supplier Part: C1525
    Datasheet: https://atta.szlcsc.com/upload/public/pdf/source/20160218/1457707763339.pdf
  schematic_page: P1
  function_block: NRST noise filter
  schematic_notes:
  - 100nF filter cap on NRST/RST line for noise immunity
- designator: C36
  type: capacitor
  value: 100nF
  footprint: C0402
  comment: 100nF
  manufacturer: SAMSUNG(三星)
  manufacturer_part: CL05B104KO5NNNC
  supplier_part: C1525
  placement:
    x_mm: 23.876
    y_mm: 36.195
    rotation_deg: 270.0
    layer: T
  pins:
    '1': GND
    '2': 3.3V_ANA
  bom_data:
    No.: '6'
    Designator: C5,C13,C16,C22,C23,C24,C31,C32,C35,C36,C37,C42,C43,C44,C45,C46,C47,C48,C50,C51
    Quantity: '20'
    Manufacturer: SAMSUNG(三星)
    Manufacturer Part: CL05B104KO5NNNC
    Comment: 100nF
    Footprint: C0402
    Mounting Style: SMT
    Supplier Part: C1525
    Datasheet: https://atta.szlcsc.com/upload/public/pdf/source/20160218/1457707763339.pdf
  schematic_page: P1
  function_block: MCU VDDA decoupling
  schematic_notes:
  - 100nF additional decoupling on MCU analog supply VDDA
- designator: C37
  type: capacitor
  value: 100nF
  footprint: C0402
  comment: 100nF
  manufacturer: SAMSUNG(三星)
  manufacturer_part: CL05B104KO5NNNC
  supplier_part: C1525
  placement:
    x_mm: 37.338
    y_mm: 36.576
    rotation_deg: 180.0
    layer: T
  pins:
    '1': GND
    '2': 3.3V
  bom_data:
    No.: '6'
    Designator: C5,C13,C16,C22,C23,C24,C31,C32,C35,C36,C37,C42,C43,C44,C45,C46,C47,C48,C50,C51
    Quantity: '20'
    Manufacturer: SAMSUNG(三星)
    Manufacturer Part: CL05B104KO5NNNC
    Comment: 100nF
    Footprint: C0402
    Mounting Style: SMT
    Supplier Part: C1525
    Datasheet: https://atta.szlcsc.com/upload/public/pdf/source/20160218/1457707763339.pdf
  schematic_page: P1
  function_block: 3.3V decoupling (CPU)
  schematic_notes:
  - 100nF decoupling on 3.3V rail near MCU U12
- designator: C38
  type: capacitor
  value: 4.7nF
  footprint: C0402
  comment: 4.7nF
  manufacturer: FH(风华)
  manufacturer_part: 0402B472K500NT
  supplier_part: C1538
  placement:
    x_mm: 48.641
    y_mm: 30.861
    rotation_deg: 0.0
    layer: T
  pins:
    '1': GND
    '2': $1N254540
  bom_data:
    No.: '15'
    Designator: C38
    Quantity: '1'
    Manufacturer: FH(风华)
    Manufacturer Part: 0402B472K500NT
    Comment: 4.7nF
    Footprint: C0402
    Mounting Style: SMT
    Supplier Part: C1538
    Datasheet: https://atta.szlcsc.com/upload/public/pdf/source/20200305/C486355_26A10D38EF8C2A5C37091D0039909270.pdf
  schematic_page: P1
  function_block: USB-C shell filter capacitor
  schematic_notes:
  - 4.7nF filter cap on USB-C connector shell/case pin to GND
- designator: C39
  type: capacitor
  value: 1uF
  footprint: C0402
  comment: 1uF
  manufacturer: SAMSUNG(三星)
  manufacturer_part: CL05A105KA5NQNC
  supplier_part: C52923
  placement:
    x_mm: 28.067
    y_mm: 22.987
    rotation_deg: 180.0
    layer: T
  pins:
    '1': $2N788708
    '2': GND
  bom_data:
    No.: '9'
    Designator: C11,C21,C25,C26,C34,C39,C40,C41,C49
    Quantity: '9'
    Manufacturer: SAMSUNG(三星)
    Manufacturer Part: CL05A105KA5NQNC
    Comment: 1uF
    Footprint: C0402
    Mounting Style: SMT
    Supplier Part: C52923
    Datasheet: https://atta.szlcsc.com/upload/public/pdf/source/20160218/1457707763339.pdf
  schematic_page: P2
  function_block: SW_NEXT debounce capacitor
  schematic_notes:
  - 1uF debounce cap for SW_NEXT; RC with R29 22k gives ~20ms time constant
  - Signal passes through U14 74HC14 Schmitt inverter for clean edge
- designator: C40
  type: capacitor
  value: 1uF
  footprint: C0402
  comment: 1uF
  manufacturer: SAMSUNG(三星)
  manufacturer_part: CL05A105KA5NQNC
  supplier_part: C52923
  placement:
    x_mm: 30.988
    y_mm: 22.987
    rotation_deg: 180.0
    layer: T
  pins:
    '1': $2N788818
    '2': GND
  bom_data:
    No.: '9'
    Designator: C11,C21,C25,C26,C34,C39,C40,C41,C49
    Quantity: '9'
    Manufacturer: SAMSUNG(三星)
    Manufacturer Part: CL05A105KA5NQNC
    Comment: 1uF
    Footprint: C0402
    Mounting Style: SMT
    Supplier Part: C52923
    Datasheet: https://atta.szlcsc.com/upload/public/pdf/source/20160218/1457707763339.pdf
  schematic_page: P2
  function_block: SW_SELECT debounce capacitor
  schematic_notes:
  - 1uF debounce cap for SW_SELECT; RC with R30 22k = ~20ms
- designator: C41
  type: capacitor
  value: 1uF
  footprint: C0402
  comment: 1uF
  manufacturer: SAMSUNG(三星)
  manufacturer_part: CL05A105KA5NQNC
  supplier_part: C52923
  placement:
    x_mm: 33.909
    y_mm: 22.987
    rotation_deg: 180.0
    layer: T
  pins:
    '1': $2N788938
    '2': GND
  bom_data:
    No.: '9'
    Designator: C11,C21,C25,C26,C34,C39,C40,C41,C49
    Quantity: '9'
    Manufacturer: SAMSUNG(三星)
    Manufacturer Part: CL05A105KA5NQNC
    Comment: 1uF
    Footprint: C0402
    Mounting Style: SMT
    Supplier Part: C52923
    Datasheet: https://atta.szlcsc.com/upload/public/pdf/source/20160218/1457707763339.pdf
  schematic_page: P2
  function_block: SW_PREV debounce capacitor
  schematic_notes:
  - 1uF debounce cap for SW_PREV; RC with R31 22k = ~20ms
- designator: C42
  type: capacitor
  value: 100nF
  footprint: C0402
  comment: 100nF
  manufacturer: SAMSUNG(三星)
  manufacturer_part: CL05B104KO5NNNC
  supplier_part: C1525
  placement:
    x_mm: 12.7
    y_mm: 19.177
    rotation_deg: 0.0
    layer: T
  pins:
    '1': VIO
    '2': GND
  bom_data:
    No.: '6'
    Designator: C5,C13,C16,C22,C23,C24,C31,C32,C35,C36,C37,C42,C43,C44,C45,C46,C47,C48,C50,C51
    Quantity: '20'
    Manufacturer: SAMSUNG(三星)
    Manufacturer Part: CL05B104KO5NNNC
    Comment: 100nF
    Footprint: C0402
    Mounting Style: SMT
    Supplier Part: C1525
    Datasheet: https://atta.szlcsc.com/upload/public/pdf/source/20160218/1457707763339.pdf
  schematic_page: P3
  function_block: VIO decoupling (target interface)
  schematic_notes:
  - 100nF decoupling on VIO rail near level translator U13
- designator: C43
  type: capacitor
  value: 100nF
  footprint: C0402
  comment: 100nF
  manufacturer: SAMSUNG(三星)
  manufacturer_part: CL05B104KO5NNNC
  supplier_part: C1525
  placement:
    x_mm: 21.336
    y_mm: 16.129
    rotation_deg: 0.0
    layer: T
  pins:
    '1': 3.3V
    '2': GND
  bom_data:
    No.: '6'
    Designator: C5,C13,C16,C22,C23,C24,C31,C32,C35,C36,C37,C42,C43,C44,C45,C46,C47,C48,C50,C51
    Quantity: '20'
    Manufacturer: SAMSUNG(三星)
    Manufacturer Part: CL05B104KO5NNNC
    Comment: 100nF
    Footprint: C0402
    Mounting Style: SMT
    Supplier Part: C1525
    Datasheet: https://atta.szlcsc.com/upload/public/pdf/source/20160218/1457707763339.pdf
  schematic_page: P3
  function_block: VIO decoupling (target interface)
  schematic_notes:
  - 100nF decoupling on VIO rail near level translator U13
- designator: C44
  type: capacitor
  value: 100nF
  footprint: C0402
  comment: 100nF
  manufacturer: SAMSUNG(三星)
  manufacturer_part: CL05B104KO5NNNC
  supplier_part: C1525
  placement:
    x_mm: 23.368
    y_mm: 18.669
    rotation_deg: 270.0
    layer: T
  pins:
    '1': VIO
    '2': GND
  bom_data:
    No.: '6'
    Designator: C5,C13,C16,C22,C23,C24,C31,C32,C35,C36,C37,C42,C43,C44,C45,C46,C47,C48,C50,C51
    Quantity: '20'
    Manufacturer: SAMSUNG(三星)
    Manufacturer Part: CL05B104KO5NNNC
    Comment: 100nF
    Footprint: C0402
    Mounting Style: SMT
    Supplier Part: C1525
    Datasheet: https://atta.szlcsc.com/upload/public/pdf/source/20160218/1457707763339.pdf
  schematic_page: P3
  function_block: VIO decoupling (spare)
  schematic_notes:
  - 100nF decoupling on VIO rail; spare/unassigned area
- designator: C45
  type: capacitor
  value: 100nF
  footprint: C0402
  comment: 100nF
  manufacturer: SAMSUNG(三星)
  manufacturer_part: CL05B104KO5NNNC
  supplier_part: C1525
  placement:
    x_mm: 25.654
    y_mm: 18.542
    rotation_deg: 90.0
    layer: T
  pins:
    '1': GND
    '2': 3.3V
  bom_data:
    No.: '6'
    Designator: C5,C13,C16,C22,C23,C24,C31,C32,C35,C36,C37,C42,C43,C44,C45,C46,C47,C48,C50,C51
    Quantity: '20'
    Manufacturer: SAMSUNG(三星)
    Manufacturer Part: CL05B104KO5NNNC
    Comment: 100nF
    Footprint: C0402
    Mounting Style: SMT
    Supplier Part: C1525
    Datasheet: https://atta.szlcsc.com/upload/public/pdf/source/20160218/1457707763339.pdf
  schematic_page: P2
  function_block: IREF decoupling
  schematic_notes:
  - 100nF decoupling on IREF node for OLED current reference resistor R14
- designator: C46
  type: capacitor
  value: 100nF
  footprint: C0402
  comment: 100nF
  manufacturer: SAMSUNG(三星)
  manufacturer_part: CL05B104KO5NNNC
  supplier_part: C1525
  placement:
    x_mm: 39.624
    y_mm: 19.177
    rotation_deg: 0.0
    layer: T
  pins:
    '1': VIO
    '2': GND
  bom_data:
    No.: '6'
    Designator: C5,C13,C16,C22,C23,C24,C31,C32,C35,C36,C37,C42,C43,C44,C45,C46,C47,C48,C50,C51
    Quantity: '20'
    Manufacturer: SAMSUNG(三星)
    Manufacturer Part: CL05B104KO5NNNC
    Comment: 100nF
    Footprint: C0402
    Mounting Style: SMT
    Supplier Part: C1525
    Datasheet: https://atta.szlcsc.com/upload/public/pdf/source/20160218/1457707763339.pdf
  schematic_page: P3
  function_block: VIO decoupling (target interface)
  schematic_notes:
  - 100nF decoupling on VIO rail near level translator U15
- designator: C47
  type: capacitor
  value: 100nF
  footprint: C0402
  comment: 100nF
  manufacturer: SAMSUNG(三星)
  manufacturer_part: CL05B104KO5NNNC
  supplier_part: C1525
  placement:
    x_mm: 47.879
    y_mm: 16.891
    rotation_deg: 90.0
    layer: T
  pins:
    '1': 3.3V
    '2': GND
  bom_data:
    No.: '6'
    Designator: C5,C13,C16,C22,C23,C24,C31,C32,C35,C36,C37,C42,C43,C44,C45,C46,C47,C48,C50,C51
    Quantity: '20'
    Manufacturer: SAMSUNG(三星)
    Manufacturer Part: CL05B104KO5NNNC
    Comment: 100nF
    Footprint: C0402
    Mounting Style: SMT
    Supplier Part: C1525
    Datasheet: https://atta.szlcsc.com/upload/public/pdf/source/20160218/1457707763339.pdf
  schematic_page: P3
  function_block: 3.3V decoupling (target section)
  schematic_notes:
  - 100nF decoupling on 3.3V rail in target interface section
- designator: C48
  type: capacitor
  value: 100nF
  footprint: C0402
  comment: 100nF
  manufacturer: SAMSUNG(三星)
  manufacturer_part: CL05B104KO5NNNC
  supplier_part: C1525
  placement:
    x_mm: 8.509
    y_mm: 13.843
    rotation_deg: 90.0
    layer: T
  pins:
    '1': ADC_VIO
    '2': GND
  bom_data:
    No.: '6'
    Designator: C5,C13,C16,C22,C23,C24,C31,C32,C35,C36,C37,C42,C43,C44,C45,C46,C47,C48,C50,C51
    Quantity: '20'
    Manufacturer: SAMSUNG(三星)
    Manufacturer Part: CL05B104KO5NNNC
    Comment: 100nF
    Footprint: C0402
    Mounting Style: SMT
    Supplier Part: C1525
    Datasheet: https://atta.szlcsc.com/upload/public/pdf/source/20160218/1457707763339.pdf
  schematic_page: P3
  function_block: ADC_VIO decoupling
  schematic_notes:
  - 100nF decoupling on ADC_VIO net used to sense target VIO voltage
- designator: C49
  type: capacitor
  value: 1uF
  footprint: C0402
  comment: 1uF
  manufacturer: SAMSUNG(三星)
  manufacturer_part: CL05A105KA5NQNC
  supplier_part: C52923
  placement:
    x_mm: 19.304
    y_mm: 11.43
    rotation_deg: 90.0
    layer: T
  pins:
    '1': GND
    '2': VIO
  bom_data:
    No.: '9'
    Designator: C11,C21,C25,C26,C34,C39,C40,C41,C49
    Quantity: '9'
    Manufacturer: SAMSUNG(三星)
    Manufacturer Part: CL05A105KA5NQNC
    Comment: 1uF
    Footprint: C0402
    Mounting Style: SMT
    Supplier Part: C52923
    Datasheet: https://atta.szlcsc.com/upload/public/pdf/source/20160218/1457707763339.pdf
  schematic_page: P3
  function_block: VIO bulk decoupling
  schematic_notes:
  - 1uF bulk decoupling on VIO rail for target power domain
- designator: C50
  type: capacitor
  value: 100nF
  footprint: C0402
  comment: 100nF
  manufacturer: SAMSUNG(三星)
  manufacturer_part: CL05B104KO5NNNC
  supplier_part: C1525
  placement:
    x_mm: 21.082
    y_mm: 11.43
    rotation_deg: 270.0
    layer: T
  pins:
    '1': VIO
    '2': GND
  bom_data:
    No.: '6'
    Designator: C5,C13,C16,C22,C23,C24,C31,C32,C35,C36,C37,C42,C43,C44,C45,C46,C47,C48,C50,C51
    Quantity: '20'
    Manufacturer: SAMSUNG(三星)
    Manufacturer Part: CL05B104KO5NNNC
    Comment: 100nF
    Footprint: C0402
    Mounting Style: SMT
    Supplier Part: C1525
    Datasheet: https://atta.szlcsc.com/upload/public/pdf/source/20160218/1457707763339.pdf
  schematic_page: P3
  function_block: 3.3V decoupling (target section)
  schematic_notes:
  - 100nF decoupling on 3.3V rail in target section
- designator: C51
  type: capacitor
  value: 100nF
  footprint: C0402
  comment: 100nF
  manufacturer: SAMSUNG(三星)
  manufacturer_part: CL05B104KO5NNNC
  supplier_part: C1525
  placement:
    x_mm: 46.482
    y_mm: 11.43
    rotation_deg: 270.0
    layer: T
  pins:
    '1': VIO
    '2': GND
  bom_data:
    No.: '6'
    Designator: C5,C13,C16,C22,C23,C24,C31,C32,C35,C36,C37,C42,C43,C44,C45,C46,C47,C48,C50,C51
    Quantity: '20'
    Manufacturer: SAMSUNG(三星)
    Manufacturer Part: CL05B104KO5NNNC
    Comment: 100nF
    Footprint: C0402
    Mounting Style: SMT
    Supplier Part: C1525
    Datasheet: https://atta.szlcsc.com/upload/public/pdf/source/20160218/1457707763339.pdf
  schematic_page: P3
  function_block: VIO decoupling (target interface)
  schematic_notes:
  - 100nF decoupling on VIO rail near level translator U15
- designator: C52
  type: capacitor
  value: ''
  placement:
    x_mm: 15.875
    y_mm: 78.232
    rotation_deg: 90.0
    layer: B
  pins:
    '1': GND
    '2': CAN_GND
  schematic_page: P3
  function_block: CAN isolation barrier Y-capacitor
  schematic_notes:
  - DNP (do not populate) by default
  - 'Bridges isolation barrier: GND to CAN_GND'
  - Populate only for EMC conducted-emission debugging
  - May introduce safety/leakage issues depending on application
  - 2.2nF 400VAC rated
  alternate_parts:
  - supplier_part: C2685703
    manufacturer_part: TMY1102M
    value: 1nF 400VAC
    note: Alternate Y-cap value
  - supplier_part: C2685704
    manufacturer_part: TMY1222M
    value: 2.2nF 400VAC
    note: Same value alternate source
- designator: CN1
  type: connector
  value: SM06B-GHS-TB(LF)(SN)
  footprint: CONN-TH_SM06B-GHS-TB-LF-SN
  comment: SM06B-GHS-TB(LF)(SN)
  manufacturer: JST
  manufacturer_part: SM06B-GHS-TB(LF)(SN)
  supplier_part: C133065
  placement:
    x_mm: 17.12
    y_mm: 97.028
    rotation_deg: 180.0
    layer: T
  pins:
    '1': CAN_GND
    '2': CAN_LO
    '3': CAN_HI
    '4': CAN_LO
    '5': CAN_HI
    '6': CAN_GND
    '7': CAN_GND
    '8': CAN_GND
  bom_data:
    No.: '16'
    Designator: CN1,CN2,CN3,CN4,CN5
    Quantity: '5'
    Manufacturer: JST
    Manufacturer Part: SM06B-GHS-TB(LF)(SN)
    Comment: SM06B-GHS-TB(LF)(SN)
    Footprint: CONN-TH_SM06B-GHS-TB-LF-SN
    Mounting Style: SMT
    Supplier Part: C133065
    Datasheet: https://atta.szlcsc.com/upload/public/pdf/source/20180323/112205B2CF875947C9562BFC7B01FA26.pdf
  schematic_page: P3
  function_block: CAN bus output connector
  schematic_notes:
  - 'Isolated CAN side: CAN_HI, CAN_LO, CAN_GND, CAN_5V_OUT, CAN_5V_IN'
  - Maintain creepage and clearance across isolation barrier
  - No silkscreen in isolation barrier area
  alternate_parts:
  - supplier_part: C225129
    manufacturer_part: A1257WR-S-6P
    manufacturer: CJT(长江)
    note: CJT alternate
  - supplier_part: C51940119
    manufacturer_part: XY-SM06B-GHS-TB
    manufacturer: XYECONN(辛译)
    note: XYECONN alternate
- designator: CN2
  type: connector
  value: SM06B-GHS-TB(LF)(SN)
  footprint: CONN-TH_SM06B-GHS-TB-LF-SN
  comment: SM06B-GHS-TB(LF)(SN)
  manufacturer: JST
  manufacturer_part: SM06B-GHS-TB(LF)(SN)
  supplier_part: C133065
  placement:
    x_mm: 3.429
    y_mm: 43.434
    rotation_deg: 270.0
    layer: T
  pins:
    '1': GND
    '2': 3.3V
    '3': I2C1_SDA
    '4': I2C1_SCL
    '5': I2C3_SDA
    '6': I2C3_SCL
    '7': GND
    '8': GND
  bom_data:
    No.: '16'
    Designator: CN1,CN2,CN3,CN4,CN5
    Quantity: '5'
    Manufacturer: JST
    Manufacturer Part: SM06B-GHS-TB(LF)(SN)
    Comment: SM06B-GHS-TB(LF)(SN)
    Footprint: CONN-TH_SM06B-GHS-TB-LF-SN
    Mounting Style: SMT
    Supplier Part: C133065
    Datasheet: https://atta.szlcsc.com/upload/public/pdf/source/20180323/112205B2CF875947C9562BFC7B01FA26.pdf
  schematic_page: P2
  function_block: I2C expansion connector
  schematic_notes:
  - Exposes I2C1 (SDA/SCL) and I2C3 (SDA/SCL) plus 3.3V and GND
  - For external I2C sensors or peripherals
  alternate_parts:
  - supplier_part: C225129
    manufacturer_part: A1257WR-S-6P
    manufacturer: CJT(长江)
    note: CJT alternate
  - supplier_part: C51940119
    manufacturer_part: XY-SM06B-GHS-TB
    manufacturer: XYECONN(辛译)
    note: XYECONN alternate
- designator: CN3
  type: connector
  value: SM06B-GHS-TB(LF)(SN)
  footprint: CONN-TH_SM06B-GHS-TB-LF-SN
  comment: SM06B-GHS-TB(LF)(SN)
  manufacturer: JST
  manufacturer_part: SM06B-GHS-TB(LF)(SN)
  supplier_part: C133065
  placement:
    x_mm: 56.591
    y_mm: 20.32
    rotation_deg: 90.0
    layer: T
  pins:
    '1': 3.3V
    '2': CONSOLE_TXD
    '3': CONSOLE_RXD
    '4': SYS_SWDIO
    '5': SYS_SWCLK
    '6': GND
    '7': GND
    '8': GND
  bom_data:
    No.: '16'
    Designator: CN1,CN2,CN3,CN4,CN5
    Quantity: '5'
    Manufacturer: JST
    Manufacturer Part: SM06B-GHS-TB(LF)(SN)
    Comment: SM06B-GHS-TB(LF)(SN)
    Footprint: CONN-TH_SM06B-GHS-TB-LF-SN
    Mounting Style: SMT
    Supplier Part: C133065
    Datasheet: https://atta.szlcsc.com/upload/public/pdf/source/20180323/112205B2CF875947C9562BFC7B01FA26.pdf
  schematic_page: P1
  function_block: System SWD and console UART connector
  schematic_notes:
  - Debug header for the AT32F405 MCU itself (not the target)
  - 'Signals: SYS_SWDIO, SYS_SWCLK, CONSOLE_TXD, CONSOLE_RXD, 3.3V, GND'
  alternate_parts:
  - supplier_part: C225129
    manufacturer_part: A1257WR-S-6P
    manufacturer: CJT(长江)
    note: CJT alternate
  - supplier_part: C51940119
    manufacturer_part: XY-SM06B-GHS-TB
    manufacturer: XYECONN(辛译)
    note: XYECONN alternate
- designator: CN4
  type: connector
  value: SM06B-GHS-TB(LF)(SN)
  footprint: CONN-TH_SM06B-GHS-TB-LF-SN
  comment: SM06B-GHS-TB(LF)(SN)
  manufacturer: JST
  manufacturer_part: SM06B-GHS-TB(LF)(SN)
  supplier_part: C133065
  placement:
    x_mm: 16.764
    y_mm: 3.937
    rotation_deg: 0.0
    layer: T
  pins:
    '1': VIO
    '2': T_TXD
    '3': T_RXD
    '4': T_SWDIO
    '5': T_SWCLK
    '6': GND
    '7': GND
    '8': GND
  bom_data:
    No.: '16'
    Designator: CN1,CN2,CN3,CN4,CN5
    Quantity: '5'
    Manufacturer: JST
    Manufacturer Part: SM06B-GHS-TB(LF)(SN)
    Comment: SM06B-GHS-TB(LF)(SN)
    Footprint: CONN-TH_SM06B-GHS-TB-LF-SN
    Mounting Style: SMT
    Supplier Part: C133065
    Datasheet: https://atta.szlcsc.com/upload/public/pdf/source/20180323/112205B2CF875947C9562BFC7B01FA26.pdf
  schematic_page: P3
  function_block: Target SWD and UART connector
  schematic_notes:
  - Primary debug output to target device
  - 'Signals: VIO, T_SWDIO, T_SWCLK, T_TXD, T_RXD, GND'
  - Level-shifted by U13 SN74AVC4T774 to target VIO voltage
  alternate_parts:
  - supplier_part: C225129
    manufacturer_part: A1257WR-S-6P
    manufacturer: CJT(长江)
    note: CJT alternate
  - supplier_part: C51940119
    manufacturer_part: XY-SM06B-GHS-TB
    manufacturer: XYECONN(辛译)
    note: XYECONN alternate
- designator: CN5
  type: connector
  value: SM06B-GHS-TB(LF)(SN)
  footprint: CONN-TH_SM06B-GHS-TB-LF-SN
  comment: SM06B-GHS-TB(LF)(SN)
  manufacturer: JST
  manufacturer_part: SM06B-GHS-TB(LF)(SN)
  supplier_part: C133065
  placement:
    x_mm: 44.196
    y_mm: 3.937
    rotation_deg: 0.0
    layer: T
  pins:
    '1': VIO
    '2': T_AUX_TXD
    '3': T_AUX_RXD
    '4': T_SWO
    '5': T_RST
    '6': GND
    '7': GND
    '8': GND
  bom_data:
    No.: '16'
    Designator: CN1,CN2,CN3,CN4,CN5
    Quantity: '5'
    Manufacturer: JST
    Manufacturer Part: SM06B-GHS-TB(LF)(SN)
    Comment: SM06B-GHS-TB(LF)(SN)
    Footprint: CONN-TH_SM06B-GHS-TB-LF-SN
    Mounting Style: SMT
    Supplier Part: C133065
    Datasheet: https://atta.szlcsc.com/upload/public/pdf/source/20180323/112205B2CF875947C9562BFC7B01FA26.pdf
  schematic_page: P3
  function_block: Target AUX, SWO and RST connector
  schematic_notes:
  - 'Auxiliary target connector: T_AUX_TXD, T_AUX_RXD, T_SWO, T_RST, VIO, GND'
  - T_SWO routed to USART RX for SWO/TraceSWO capture
  - T_RST driven by MOSFET Q1 open-drain circuit
  - Level-shifted by U15 SN74AVC4T774 to target VIO voltage
  alternate_parts:
  - supplier_part: C225129
    manufacturer_part: A1257WR-S-6P
    manufacturer: CJT(长江)
    note: CJT alternate
  - supplier_part: C51940119
    manufacturer_part: XY-SM06B-GHS-TB
    manufacturer: XYECONN(辛译)
    note: XYECONN alternate
- designator: D1
  type: diode
  value: ESDCAN03-2BWY
  footprint: SOT-323-3_L2.0-W1.3-P1.30-LS2.1-BR
  comment: ESDCAN03-2BWY
  manufacturer: ST(意法半导体)
  manufacturer_part: ESDCAN03-2BWY
  supplier_part: C1973833
  placement:
    x_mm: 15.875
    y_mm: 91.948
    rotation_deg: 90.0
    layer: T
  pins:
    '1': CAN_LO
    '2': CAN_HI
    '3': CAN_GND
  bom_data:
    No.: '17'
    Designator: D1
    Quantity: '1'
    Manufacturer: ST(意法半导体)
    Manufacturer Part: ESDCAN03-2BWY
    Comment: ESDCAN03-2BWY
    Footprint: SOT-323-3_L2.0-W1.3-P1.30-LS2.1-BR
    Mounting Style: SMT
    Supplier Part: C1973833
    Datasheet: https://atta.szlcsc.com/upload/public/pdf/source/20210601/EE22EC2D769ED57BA217B6DB28AAC84F.pdf
  schematic_page: P3
  function_block: CAN bus ESD protection
  schematic_notes:
  - 'ST ESDCAN03-2BWY: bidirectional dual-rail TVS on CAN_HI and CAN_LO'
  - Clamps CAN bus transients; low capacitance for signal integrity
- designator: D2
  type: diode
  value: H5VU25U
  footprint: DFN2510-10_L2.5-W1.0-P0.50-BL
  comment: H5VU25U
  manufacturer: 宏迦橙
  manufacturer_part: H5VU25U
  supplier_part: C7420374
  placement:
    x_mm: 40.005
    y_mm: 76.2
    rotation_deg: 0.0
    layer: T
  pins:
    '1': SD_CS
    '2': GND
    '3': GND
    '4': GND
    '5': SPI2_MOSI
    '6': SPI2_MOSI
    '7': GND
    '8': GND
    '9': GND
    '10': SD_CS
  bom_data:
    No.: '18'
    Designator: D2,D3,D4,D7,D9,D12,D17
    Quantity: '7'
    Manufacturer: 宏迦橙
    Manufacturer Part: H5VU25U
    Comment: H5VU25U
    Footprint: DFN2510-10_L2.5-W1.0-P0.50-BL
    Mounting Style: SMT
    Supplier Part: C7420374
    Datasheet: https://atta.szlcsc.com/upload/public/pdf/source/20230630/91FD1DB17AB88B6832D3039FAE61FF10.pdf
  schematic_page: P2
  function_block: SD card SPI ESD protection
  schematic_notes:
  - H5VU25U 10-pin dual-rail ESD array on SD_CS and SPI2_MOSI
- designator: D3
  type: diode
  value: H5VU25U
  footprint: DFN2510-10_L2.5-W1.0-P0.50-BL
  comment: H5VU25U
  manufacturer: 宏迦橙
  manufacturer_part: H5VU25U
  supplier_part: C7420374
  placement:
    x_mm: 44.811
    y_mm: 78.232
    rotation_deg: 0.0
    layer: T
  pins:
    '1': SPI2_CLK
    '2': GND
    '3': GND
    '4': SPI2_MISO
    '5': SD_DETECT
    '6': SD_DETECT
    '7': SPI2_MISO
    '8': GND
    '9': GND
    '10': SPI2_CLK
  bom_data:
    No.: '18'
    Designator: D2,D3,D4,D7,D9,D12,D17
    Quantity: '7'
    Manufacturer: 宏迦橙
    Manufacturer Part: H5VU25U
    Comment: H5VU25U
    Footprint: DFN2510-10_L2.5-W1.0-P0.50-BL
    Mounting Style: SMT
    Supplier Part: C7420374
    Datasheet: https://atta.szlcsc.com/upload/public/pdf/source/20230630/91FD1DB17AB88B6832D3039FAE61FF10.pdf
  schematic_page: P2
  function_block: SD card SPI ESD protection
  schematic_notes:
  - H5VU25U ESD array on SPI2_CLK, SPI2_MISO, SD_DETECT
- designator: D4
  type: diode
  value: H5VU25U
  footprint: DFN2510-10_L2.5-W1.0-P0.50-BL
  comment: H5VU25U
  manufacturer: 宏迦橙
  manufacturer_part: H5VU25U
  supplier_part: C7420374
  placement:
    x_mm: 8.382
    y_mm: 42.164
    rotation_deg: 270.0
    layer: T
  pins:
    '1': I2C1_SDA
    '2': I2C1_SCL
    '3': GND
    '4': I2C3_SDA
    '5': I2C3_SCL
    '6': I2C3_SCL
    '7': I2C3_SDA
    '8': GND
    '9': I2C1_SCL
    '10': I2C1_SDA
  bom_data:
    No.: '18'
    Designator: D2,D3,D4,D7,D9,D12,D17
    Quantity: '7'
    Manufacturer: 宏迦橙
    Manufacturer Part: H5VU25U
    Comment: H5VU25U
    Footprint: DFN2510-10_L2.5-W1.0-P0.50-BL
    Mounting Style: SMT
    Supplier Part: C7420374
    Datasheet: https://atta.szlcsc.com/upload/public/pdf/source/20230630/91FD1DB17AB88B6832D3039FAE61FF10.pdf
  schematic_page: P2
  function_block: I2C connector ESD protection
  schematic_notes:
  - H5VU25U ESD array on I2C1_SCL, I2C1_SDA, I2C3_SCL, I2C3_SDA at CN2
- designator: D5
  type: diode
  value: SMF5.0A
  footprint: SOD-123FL_L2.7-W1.8-LS3.8-RD
  comment: SMF5.0A
  manufacturer: R+O(宏嘉诚)
  manufacturer_part: SMF5.0A
  supplier_part: C19077497
  placement:
    x_mm: 49.784
    y_mm: 42.164
    rotation_deg: 0.0
    layer: T
  pins:
    '1': HS_VBUS
    '2': GND
  bom_data:
    No.: '19'
    Designator: D5
    Quantity: '1'
    Manufacturer: R+O(宏嘉诚)
    Manufacturer Part: SMF5.0A
    Comment: SMF5.0A
    Footprint: SOD-123FL_L2.7-W1.8-LS3.8-RD
    Mounting Style: SMT
    Supplier Part: C19077497
    Datasheet: https://item.szlcsc.com/datasheet/SMF5.0A/20275582.html
  schematic_page: P1
  function_block: USB VBUS TVS clamp
  schematic_notes:
  - SMF5.0A unidirectional TVS on HS_VBUS upstream of polyfuse U11
  - Clamps VBUS transients to protect USB circuitry
- designator: D6
  type: diode
  value: H5VL10B
  footprint: SOD-882_L1.0-W0.6-BI
  comment: H5VL10B
  manufacturer: 宏迦橙
  manufacturer_part: H5VL10B
  supplier_part: C7420372
  placement:
    x_mm: 5.588
    y_mm: 32.766
    rotation_deg: 90.0
    layer: T
  pins:
    '1': GND
    '2': BOOT0
  bom_data:
    No.: '20'
    Designator: D6,D8,D10,D11,D13,D14,D15,D16
    Quantity: '8'
    Manufacturer: 宏迦橙
    Manufacturer Part: H5VL10B
    Comment: H5VL10B
    Footprint: SOD-882_L1.0-W0.6-BI
    Mounting Style: SMT
    Supplier Part: C7420372
    Datasheet: https://atta.szlcsc.com/upload/public/pdf/source/20230630/5024ECFEAD3C9801B07A8DBB967AB462.pdf
  schematic_page: P1
  function_block: BOOT0 ESD protection
  schematic_notes:
  - H5VL10B low-capacitance diode on BOOT0 line
- designator: D7
  type: diode
  value: H5VU25U
  footprint: DFN2510-10_L2.5-W1.0-P0.50-BL
  comment: H5VU25U
  manufacturer: 宏迦橙
  manufacturer_part: H5VU25U
  supplier_part: C7420374
  placement:
    x_mm: 45.72
    y_mm: 34.95
    rotation_deg: 270.0
    layer: T
  pins:
    '1': HS_DP
    '2': HS_DM
    '3': GND
    '4': GND
    '5': GND
    '6': GND
    '7': GND
    '8': GND
    '9': HS_DM
    '10': HS_DP
  bom_data:
    No.: '18'
    Designator: D2,D3,D4,D7,D9,D12,D17
    Quantity: '7'
    Manufacturer: 宏迦橙
    Manufacturer Part: H5VU25U
    Comment: H5VU25U
    Footprint: DFN2510-10_L2.5-W1.0-P0.50-BL
    Mounting Style: SMT
    Supplier Part: C7420374
    Datasheet: https://atta.szlcsc.com/upload/public/pdf/source/20230630/91FD1DB17AB88B6832D3039FAE61FF10.pdf
  schematic_page: P1
  function_block: USB HS data lines ESD protection
  schematic_notes:
  - H5VU25U ESD array on HS_DP and HS_DM USB high-speed data lines
  - Low capacitance critical for USB-HS signal integrity
- designator: D8
  type: diode
  value: H5VL10B
  footprint: SOD-882_L1.0-W0.6-BI
  comment: H5VL10B
  manufacturer: 宏迦橙
  manufacturer_part: H5VL10B
  supplier_part: C7420372
  placement:
    x_mm: 5.588
    y_mm: 23.749
    rotation_deg: 90.0
    layer: T
  pins:
    '1': GND
    '2': RST
  bom_data:
    No.: '20'
    Designator: D6,D8,D10,D11,D13,D14,D15,D16
    Quantity: '8'
    Manufacturer: 宏迦橙
    Manufacturer Part: H5VL10B
    Comment: H5VL10B
    Footprint: SOD-882_L1.0-W0.6-BI
    Mounting Style: SMT
    Supplier Part: C7420372
    Datasheet: https://atta.szlcsc.com/upload/public/pdf/source/20230630/5024ECFEAD3C9801B07A8DBB967AB462.pdf
  schematic_page: P1
  function_block: NRST ESD protection
  schematic_notes:
  - H5VL10B diode on MCU NRST/RST line
- designator: D9
  type: diode
  value: H5VU25U
  footprint: DFN2510-10_L2.5-W1.0-P0.50-BL
  comment: H5VU25U
  manufacturer: 宏迦橙
  manufacturer_part: H5VU25U
  supplier_part: C7420374
  placement:
    x_mm: 51.562
    y_mm: 20.32
    rotation_deg: 270.0
    layer: T
  pins:
    '1': SYS_SWCLK
    '2': SYS_SWDIO
    '3': GND
    '4': CONSOLE_RXD
    '5': CONSOLE_TXD
    '6': CONSOLE_TXD
    '7': CONSOLE_RXD
    '8': GND
    '9': SYS_SWDIO
    '10': SYS_SWCLK
  bom_data:
    No.: '18'
    Designator: D2,D3,D4,D7,D9,D12,D17
    Quantity: '7'
    Manufacturer: 宏迦橙
    Manufacturer Part: H5VU25U
    Comment: H5VU25U
    Footprint: DFN2510-10_L2.5-W1.0-P0.50-BL
    Mounting Style: SMT
    Supplier Part: C7420374
    Datasheet: https://atta.szlcsc.com/upload/public/pdf/source/20230630/91FD1DB17AB88B6832D3039FAE61FF10.pdf
  schematic_page: P1
  function_block: System SWD ESD protection
  schematic_notes:
  - H5VU25U ESD array on SYS_SWCLK and SYS_SWDIO at CN3
- designator: D10
  type: diode
  value: H5VL10B
  footprint: SOD-882_L1.0-W0.6-BI
  comment: H5VL10B
  manufacturer: 宏迦橙
  manufacturer_part: H5VL10B
  supplier_part: C7420372
  placement:
    x_mm: 10.414
    y_mm: 13.716
    rotation_deg: 270.0
    layer: T
  pins:
    '1': GND
    '2': ADC_VIO
  bom_data:
    No.: '20'
    Designator: D6,D8,D10,D11,D13,D14,D15,D16
    Quantity: '8'
    Manufacturer: 宏迦橙
    Manufacturer Part: H5VL10B
    Comment: H5VL10B
    Footprint: SOD-882_L1.0-W0.6-BI
    Mounting Style: SMT
    Supplier Part: C7420372
    Datasheet: https://atta.szlcsc.com/upload/public/pdf/source/20230630/5024ECFEAD3C9801B07A8DBB967AB462.pdf
  schematic_page: P3
  function_block: ADC_VIO ESD protection
  schematic_notes:
  - H5VL10B diode on ADC_VIO target voltage sense line
- designator: D11
  type: diode
  value: H5VL10B
  footprint: SOD-882_L1.0-W0.6-BI
  comment: H5VL10B
  manufacturer: 宏迦橙
  manufacturer_part: H5VL10B
  supplier_part: C7420372
  placement:
    x_mm: 13.31
    y_mm: 8.941
    rotation_deg: 0.0
    layer: T
  pins:
    '1': GND
    '2': VIO
  bom_data:
    No.: '20'
    Designator: D6,D8,D10,D11,D13,D14,D15,D16
    Quantity: '8'
    Manufacturer: 宏迦橙
    Manufacturer Part: H5VL10B
    Comment: H5VL10B
    Footprint: SOD-882_L1.0-W0.6-BI
    Mounting Style: SMT
    Supplier Part: C7420372
    Datasheet: https://atta.szlcsc.com/upload/public/pdf/source/20230630/5024ECFEAD3C9801B07A8DBB967AB462.pdf
  schematic_page: P3
  function_block: VIO rail ESD protection
  schematic_notes:
  - H5VL10B diode on VIO rail near target interface
- designator: D12
  type: diode
  value: H5VU25U
  footprint: DFN2510-10_L2.5-W1.0-P0.50-BL
  comment: H5VU25U
  manufacturer: 宏迦橙
  manufacturer_part: H5VU25U
  supplier_part: C7420374
  placement:
    x_mm: 16.764
    y_mm: 8.89
    rotation_deg: 180.0
    layer: T
  pins:
    '1': T_SWCLK
    '2': T_SWDIO
    '3': GND
    '4': T_RXD
    '5': T_TXD
    '6': T_TXD
    '7': T_RXD
    '8': GND
    '9': T_SWDIO
    '10': T_SWCLK
  bom_data:
    No.: '18'
    Designator: D2,D3,D4,D7,D9,D12,D17
    Quantity: '7'
    Manufacturer: 宏迦橙
    Manufacturer Part: H5VU25U
    Comment: H5VU25U
    Footprint: DFN2510-10_L2.5-W1.0-P0.50-BL
    Mounting Style: SMT
    Supplier Part: C7420374
    Datasheet: https://atta.szlcsc.com/upload/public/pdf/source/20230630/91FD1DB17AB88B6832D3039FAE61FF10.pdf
  schematic_page: P3
  function_block: Target SWD connector ESD protection
  schematic_notes:
  - H5VU25U ESD array on T_SWCLK, T_SWDIO, T_RXD, T_TXD at CN4
- designator: D13
  type: diode
  value: H5VL10B
  footprint: SOD-882_L1.0-W0.6-BI
  comment: H5VL10B
  manufacturer: 宏迦橙
  manufacturer_part: H5VL10B
  supplier_part: C7420372
  placement:
    x_mm: 27.813
    y_mm: 9.525
    rotation_deg: 180.0
    layer: T
  pins:
    '1': GND
    '2': SW_NEXT
  bom_data:
    No.: '20'
    Designator: D6,D8,D10,D11,D13,D14,D15,D16
    Quantity: '8'
    Manufacturer: 宏迦橙
    Manufacturer Part: H5VL10B
    Comment: H5VL10B
    Footprint: SOD-882_L1.0-W0.6-BI
    Mounting Style: SMT
    Supplier Part: C7420372
    Datasheet: https://atta.szlcsc.com/upload/public/pdf/source/20230630/5024ECFEAD3C9801B07A8DBB967AB462.pdf
  schematic_page: P2
  function_block: SW_NEXT clamp diode
  schematic_notes:
  - H5VL10B diode on SW_NEXT encoder signal line
- designator: D14
  type: diode
  value: H5VL10B
  footprint: SOD-882_L1.0-W0.6-BI
  comment: H5VL10B
  manufacturer: 宏迦橙
  manufacturer_part: H5VL10B
  supplier_part: C7420372
  placement:
    x_mm: 30.353
    y_mm: 9.525
    rotation_deg: 180.0
    layer: T
  pins:
    '1': GND
    '2': SW_SELECT
  bom_data:
    No.: '20'
    Designator: D6,D8,D10,D11,D13,D14,D15,D16
    Quantity: '8'
    Manufacturer: 宏迦橙
    Manufacturer Part: H5VL10B
    Comment: H5VL10B
    Footprint: SOD-882_L1.0-W0.6-BI
    Mounting Style: SMT
    Supplier Part: C7420372
    Datasheet: https://atta.szlcsc.com/upload/public/pdf/source/20230630/5024ECFEAD3C9801B07A8DBB967AB462.pdf
  schematic_page: P2
  function_block: SW_SELECT clamp diode
  schematic_notes:
  - H5VL10B diode on SW_SELECT encoder signal line
- designator: D15
  type: diode
  value: H5VL10B
  footprint: SOD-882_L1.0-W0.6-BI
  comment: H5VL10B
  manufacturer: 宏迦橙
  manufacturer_part: H5VL10B
  supplier_part: C7420372
  placement:
    x_mm: 32.893
    y_mm: 9.525
    rotation_deg: 180.0
    layer: T
  pins:
    '1': GND
    '2': SW_PREV
  bom_data:
    No.: '20'
    Designator: D6,D8,D10,D11,D13,D14,D15,D16
    Quantity: '8'
    Manufacturer: 宏迦橙
    Manufacturer Part: H5VL10B
    Comment: H5VL10B
    Footprint: SOD-882_L1.0-W0.6-BI
    Mounting Style: SMT
    Supplier Part: C7420372
    Datasheet: https://atta.szlcsc.com/upload/public/pdf/source/20230630/5024ECFEAD3C9801B07A8DBB967AB462.pdf
  schematic_page: P2
  function_block: SW_PREV clamp diode
  schematic_notes:
  - H5VL10B diode on SW_PREV encoder signal line
- designator: D16
  type: diode
  value: H5VL10B
  footprint: SOD-882_L1.0-W0.6-BI
  comment: H5VL10B
  manufacturer: 宏迦橙
  manufacturer_part: H5VL10B
  supplier_part: C7420372
  placement:
    x_mm: 40.767
    y_mm: 8.89
    rotation_deg: 0.0
    layer: T
  pins:
    '1': GND
    '2': VIO
  bom_data:
    No.: '20'
    Designator: D6,D8,D10,D11,D13,D14,D15,D16
    Quantity: '8'
    Manufacturer: 宏迦橙
    Manufacturer Part: H5VL10B
    Comment: H5VL10B
    Footprint: SOD-882_L1.0-W0.6-BI
    Mounting Style: SMT
    Supplier Part: C7420372
    Datasheet: https://atta.szlcsc.com/upload/public/pdf/source/20230630/5024ECFEAD3C9801B07A8DBB967AB462.pdf
  schematic_page: P3
  function_block: VIO rail ESD protection (AUX)
  schematic_notes:
  - H5VL10B diode on VIO rail near AUX target interface
- designator: D17
  type: diode
  value: H5VU25U
  footprint: DFN2510-10_L2.5-W1.0-P0.50-BL
  comment: H5VU25U
  manufacturer: 宏迦橙
  manufacturer_part: H5VU25U
  supplier_part: C7420374
  placement:
    x_mm: 44.196
    y_mm: 8.89
    rotation_deg: 180.0
    layer: T
  pins:
    '1': T_RST
    '2': T_SWO
    '3': GND
    '4': T_AUX_RXD
    '5': T_AUX_TXD
    '6': T_AUX_TXD
    '7': T_AUX_RXD
    '8': GND
    '9': T_SWO
    '10': T_RST
  bom_data:
    No.: '18'
    Designator: D2,D3,D4,D7,D9,D12,D17
    Quantity: '7'
    Manufacturer: 宏迦橙
    Manufacturer Part: H5VU25U
    Comment: H5VU25U
    Footprint: DFN2510-10_L2.5-W1.0-P0.50-BL
    Mounting Style: SMT
    Supplier Part: C7420374
    Datasheet: https://atta.szlcsc.com/upload/public/pdf/source/20230630/91FD1DB17AB88B6832D3039FAE61FF10.pdf
  schematic_page: P3
  function_block: Target AUX connector ESD protection
  schematic_notes:
  - H5VU25U ESD array on T_AUX_TXD, T_AUX_RXD, T_SWO, T_RST at CN5
- designator: FPC1
  type: unknown
  value: AFC07-S12ECA-00
  footprint: FPC-SMD_12P-P0.50_AFC07-S12ECA-00
  comment: AFC07-S12ECA-00
  manufacturer: JS(钜硕电子)
  manufacturer_part: AFC07-S12ECA-00
  supplier_part: C262585
  placement:
    x_mm: 30.48
    y_mm: 68.633
    rotation_deg: 180.0
    layer: T
  pins:
    '1': GND
    '2': 12V
    '3': SPI2_MOSI
    '4': SPI2_CLK
    '5': DISP_DC
    '6': DISP_RST
    '7': DISP_CS
    '8': IREF
    '9': 3.3V
    '10': VCOMH
    '11': 12V
    '12': GND
    '13': GND
    '14': GND
  bom_data:
    No.: '21'
    Designator: FPC1
    Quantity: '1'
    Manufacturer: JS(钜硕电子)
    Manufacturer Part: AFC07-S12ECA-00
    Comment: AFC07-S12ECA-00
    Footprint: FPC-SMD_12P-P0.50_AFC07-S12ECA-00
    Mounting Style: SMT
    Supplier Part: C262585
    Datasheet: https://atta.szlcsc.com/upload/public/pdf/source/20190726/C11082_A2E7B12387019CE4314BB5199EE0FDF4.pdf
  schematic_page: P2
  function_block: OLED display FPC connector
  schematic_notes:
  - 'AFC07-S12ECA-00: 12-pin FPC for OLED display'
  - Carries SPI2_CLK, SPI2_MOSI, DISP_CS, DISP_DC, DISP_RST, 3.3V, 12V, VCOMH, IREF,
    GND
  - 'Display: ZJY150-2828KSWKG03 (28x28mm OLED)'
  - 12V for OLED charge pump supplied by boost converter U7
- designator: L1
  type: inductor
  value: ACT1210-510-2P-TL00
  footprint: FILTER-SMD_4P-L3.2-W2.5-BL_ACT1210
  comment: ACT1210-510-2P-TL00
  manufacturer: TDK
  manufacturer_part: ACT1210-510-2P-TL00
  supplier_part: C95572
  placement:
    x_mm: 15.875
    y_mm: 87.376
    rotation_deg: 0.0
    layer: T
  pins:
    '1': $3N53774
    '2': $3N53786
    '3': CAN_LO
    '4': CAN_HI
  bom_data:
    No.: '22'
    Designator: L1
    Quantity: '1'
    Manufacturer: TDK
    Manufacturer Part: ACT1210-510-2P-TL00
    Comment: ACT1210-510-2P-TL00
    Footprint: FILTER-SMD_4P-L3.2-W2.5-BL_ACT1210
    Mounting Style: SMT
    Supplier Part: C95572
    Datasheet: https://item.szlcsc.com/datasheet/ACT1210-510-2P-TL00/96776.html
  schematic_page: P3
  function_block: CAN bus common-mode choke
  schematic_notes:
  - 'ACT1210-510-2P-TL00: dual-winding common-mode choke on CAN_HI and CAN_LO'
  - 510 ohm impedance at 100MHz; suppresses common-mode EMI on CAN bus
  - 'For CAN-FD upgrade: replace with a CAN-FD rated choke (flat differential-mode
    impedance to 20-50MHz)'
- designator: L2
  type: inductor
  value: GZ1608D601TF
  footprint: L0603
  comment: GZ1608D601TF
  manufacturer: Sunlord(顺络)
  manufacturer_part: GZ1608D601TF
  supplier_part: C1002
  placement:
    x_mm: 19.304
    y_mm: 87.63
    rotation_deg: 180.0
    layer: T
  pins:
    '1': CAN_5V_OUT
    '2': CAN_5V_IN
  bom_data:
    No.: '23'
    Designator: L2
    Quantity: '1'
    Manufacturer: Sunlord(顺络)
    Manufacturer Part: GZ1608D601TF
    Comment: GZ1608D601TF
    Footprint: L0603
    Mounting Style: SMT
    Supplier Part: C1002
    Datasheet: https://atta.szlcsc.com/upload/public/pdf/source/20241120/893429B990C3BA07384E734821D2F218.pdf
  schematic_page: P3
  function_block: CAN isolated supply ferrite bead
  schematic_notes:
  - GZ1608D601TF ferrite bead on CAN_5V_IN to U3 isolated supply pin
  - Reduces switching noise coupling into isolated CAN domain
- designator: L3
  type: inductor
  value: 1uH
  footprint: IND-SMD_L2.5-W2.0-A
  comment: 1uH
  manufacturer: TDK
  manufacturer_part: TFM252012ALM-1R0MTAA
  supplier_part: C433057
  placement:
    x_mm: 53.594
    y_mm: 80.391
    rotation_deg: 90.0
    layer: T
  pins:
    '1': VSW
    '2': 3.3V
  bom_data:
    No.: '24'
    Designator: L3
    Quantity: '1'
    Manufacturer: TDK
    Manufacturer Part: TFM252012ALM-1R0MTAA
    Comment: 1uH
    Footprint: IND-SMD_L2.5-W2.0-A
    Mounting Style: SMT
    Supplier Part: C433057
  schematic_page: P1
  function_block: 3.3V buck converter output inductor
  schematic_notes:
  - 1uH output inductor for TLV62569 3.3V buck converter U4
  - 'Schematic specifies: I_sat >= 1.2A, DCR <= 200 mohm'
- designator: L4
  type: inductor
  value: 10uH
  footprint: IND-SMD_L4.1-W4.1_FTC404020S
  comment: 10uH
  manufacturer: cjiang(长江微电)
  manufacturer_part: FTC404020S100MGCA
  supplier_part: C39676074
  placement:
    x_mm: 54.61
    y_mm: 58.166
    rotation_deg: 0.0
    layer: T
  pins:
    '1': 5V
    '2': $2N576115
  bom_data:
    No.: '25'
    Designator: L4
    Quantity: '1'
    Manufacturer: cjiang(长江微电)
    Manufacturer Part: FTC404020S100MGCA
    Comment: 10uH
    Footprint: IND-SMD_L4.1-W4.1_FTC404020S
    Mounting Style: SMT
    Supplier Part: C39676074
    Datasheet: https://item.szlcsc.com/datasheet/FTC404020S100MGCA/41398075.html
  schematic_page: P2
  function_block: 12V boost converter output inductor
  schematic_notes:
  - 10uH output inductor for TLV61046 12V boost converter U7
- designator: L5
  type: inductor
  value: 10uH
  footprint: L0603
  comment: 10uH
  manufacturer: Sunlord(顺络)
  manufacturer_part: SDFL1608S100KTF
  supplier_part: C1035
  placement:
    x_mm: 16.51
    y_mm: 33.528
    rotation_deg: 270.0
    layer: T
  pins:
    '1': 3.3V
    '2': 3.3V_ANA
  bom_data:
    No.: '26'
    Designator: L5
    Quantity: '1'
    Manufacturer: Sunlord(顺络)
    Manufacturer Part: SDFL1608S100KTF
    Comment: 10uH
    Footprint: L0603
    Mounting Style: SMT
    Supplier Part: C1035
  schematic_page: P1
  function_block: 3.3V analog supply filter inductor
  schematic_notes:
  - 10uH inductor forming LC filter between 3.3V digital and 3.3V_ANA
  - 3.3V_ANA supplies MCU VDDA for ADC noise isolation
- designator: LED1
  type: led
  value: LTST-S270KGKT
  footprint: LED-SMD_L1.7-W0.6-RD
  comment: LTST-S270KGKT
  manufacturer: LITEON(光宝)
  manufacturer_part: LTST-S270KGKT
  supplier_part: C125113
  placement:
    x_mm: 1.651
    y_mm: 13.97
    rotation_deg: 90.0
    layer: T
  pins:
    '1': $1N206167
    '2': 3.3V
  bom_data:
    No.: '27'
    Designator: LED1
    Quantity: '1'
    Manufacturer: LITEON(光宝)
    Manufacturer Part: LTST-S270KGKT
    Comment: LTST-S270KGKT
    Footprint: LED-SMD_L1.7-W0.6-RD
    Mounting Style: SMT
    Supplier Part: C125113
    Datasheet: https://atta.szlcsc.com/upload/public/pdf/source/20180104/C125113_15150602232371230485.pdf
  schematic_page: P1
  function_block: Status LED
  schematic_notes:
  - 'LTST-S270KGKT: green side-emitting LED'
  - Driven by MCU pin PC6 (LED0 net) via R38 150 ohm current limiter
  - Side-emitting for panel-mount visibility through enclosure
  alternate_parts:
  - supplier_part: C2286
    manufacturer_part: KT-0603R
    note: JLCPCB basic library alternate; different colour and emission angle
- designator: M1
  type: mechanical
  value: ''
  placement:
    x_mm: 5.0
    y_mm: 95.508
    rotation_deg: 0.0
    layer: T
  pins:
    '1': CAN_GND
  schematic_page: P1
  function_block: Mounting hole 3.2mm
  schematic_notes:
  - M3 clearance hole for enclosure fastener
- designator: M2
  type: mechanical
  value: ''
  placement:
    x_mm: 55.0
    y_mm: 95.508
    rotation_deg: 0.0
    layer: T
  pins:
    '1': GND
  schematic_page: P1
  function_block: Mounting hole 3.2mm
  schematic_notes:
  - M3 clearance hole for enclosure fastener
- designator: M3
  type: mechanical
  value: ''
  placement:
    x_mm: 5.0
    y_mm: 5.508
    rotation_deg: 0.0
    layer: T
  pins:
    '1': GND
  schematic_page: P1
  function_block: Mounting hole 3.2mm
  schematic_notes:
  - M3 clearance hole for enclosure fastener
- designator: M4
  type: mechanical
  value: ''
  placement:
    x_mm: 55.0
    y_mm: 5.508
    rotation_deg: 0.0
    layer: T
  pins:
    '1': GND
  schematic_page: P1
  function_block: Mounting hole 3.2mm
  schematic_notes:
  - M3 clearance hole for enclosure fastener
- designator: OLED1
  type: unknown
  value: ZJY150-2828KSWKG03
  footprint: OLED-ZJY150-2828KSWKG03
  comment: ZJY150-2828KSWKG03
  manufacturer: Zhengzhou Zhongjingyuan(中景园)
  manufacturer_part: ZJY150-2828KSWKG03
  supplier_part: https://item.taobao.com/item.htm?id=756962244579
  placement:
    x_mm: 30.48
    y_mm: 40.538
    rotation_deg: 0.0
    layer: B
  bom_data:
    No.: '28'
    Designator: OLED1
    Quantity: '1'
    Manufacturer: Zhengzhou Zhongjingyuan(中景园)
    Manufacturer Part: ZJY150-2828KSWKG03
    Comment: ZJY150-2828KSWKG03
    Footprint: OLED-ZJY150-2828KSWKG03
    Mounting Style: SMT
    Supplier Part: https://item.taobao.com/item.htm?id=756962244579
  schematic_page: P2
  function_block: OLED display module
  schematic_notes:
  - 'ZJY150-2828KSWKG03: 28x28mm OLED display'
  - DNS (do not solder) - user installs with double-sided adhesive tape and FPC connector
  - Connected via FPC1 connector
  - 12V charge pump supply from U7 boost converter
- designator: Q1
  type: transistor
  value: AO3400A
  footprint: SOT-23-3_L2.9-W1.3-P1.90-LS2.4-BR
  comment: AO3400A
  manufacturer: AOS
  manufacturer_part: AO3400A
  supplier_part: C20917
  placement:
    x_mm: 51.562
    y_mm: 12.446
    rotation_deg: 90.0
    layer: T
  pins:
    '1': $3N5450
    '2': GND
    '3': T_RST
  bom_data:
    No.: '29'
    Designator: Q1
    Quantity: '1'
    Manufacturer: AOS
    Manufacturer Part: AO3400A
    Comment: AO3400A
    Footprint: SOT-23-3_L2.9-W1.3-P1.90-LS2.4-BR
    Mounting Style: SMT
    Supplier Part: C20917
    Datasheet: https://atta.szlcsc.com/upload/public/pdf/source/20140107/1457706668533.pdf
  schematic_page: P3
  function_block: Target reset open-drain driver
  schematic_notes:
  - AO3400A N-channel MOSFET for open-drain target reset output (T_RST)
  - Gate driven by MCU T_RST_OUT via R26 33 ohm series resistor
  - R37 100k pull-up to VIO holds T_RST high (inactive) when not driven
  - R46 10k pull-down on gate ensures MOSFET off when MCU is tristated
  - Allows MCU to both assert and sense T_RST bidirectionally
- designator: R1
  type: resistor
  value: 33Ω
  footprint: R0402
  comment: 33Ω
  manufacturer: UNI-ROYAL(厚声)
  manufacturer_part: 0402WGF330JTCE
  supplier_part: C25105
  placement:
    x_mm: 46.228
    y_mm: 82.677
    rotation_deg: 90.0
    layer: T
  pins:
    '1': SPI2_MISO
    '2': $2N508660
  bom_data:
    No.: '30'
    Designator: R1,R5,R13,R19,R26
    Quantity: '5'
    Manufacturer: UNI-ROYAL(厚声)
    Manufacturer Part: 0402WGF330JTCE
    Comment: 33Ω
    Footprint: R0402
    Mounting Style: SMT
    Supplier Part: C25105
    Datasheet: https://atta.szlcsc.com/upload/public/pdf/source/20200306/C422600_1E6D84923E4A46A82E41ADD87F860B5C.pdf
  schematic_page: P2
  function_block: SD card MISO series termination
  schematic_notes:
  - 33 ohm series termination on SPI2_MISO from SD card U1
- designator: R2
  type: resistor
  value: 47kΩ
  footprint: R0402
  comment: 47kΩ
  manufacturer: UNI-ROYAL(厚声)
  manufacturer_part: 0402WGF4702TCE
  supplier_part: C25792
  placement:
    x_mm: 47.371
    y_mm: 78.232
    rotation_deg: 90.0
    layer: T
  pins:
    '1': GND
    '2': SD_ON
  bom_data:
    No.: '31'
    Designator: R2,R3,R6,R7,R8,R41
    Quantity: '6'
    Manufacturer: UNI-ROYAL(厚声)
    Manufacturer Part: 0402WGF4702TCE
    Comment: 47kΩ
    Footprint: R0402
    Mounting Style: SMT
    Supplier Part: C25792
    Datasheet: https://atta.szlcsc.com/upload/public/pdf/source/20200306/C422600_1E6D84923E4A46A82E41ADD87F860B5C.pdf
  schematic_page: P2
  function_block: SD_ON pull-down
  schematic_notes:
  - 47k pull-down on SD_ON; SD card unpowered at startup until MCU enables it
- designator: R3
  type: resistor
  value: 47kΩ
  footprint: R0402
  comment: 47kΩ
  manufacturer: UNI-ROYAL(厚声)
  manufacturer_part: 0402WGF4702TCE
  supplier_part: C25792
  placement:
    x_mm: 46.609
    y_mm: 73.914
    rotation_deg: 180.0
    layer: T
  pins:
    '1': SD_DETECT
    '2': 3.3V
  bom_data:
    No.: '31'
    Designator: R2,R3,R6,R7,R8,R41
    Quantity: '6'
    Manufacturer: UNI-ROYAL(厚声)
    Manufacturer Part: 0402WGF4702TCE
    Comment: 47kΩ
    Footprint: R0402
    Mounting Style: SMT
    Supplier Part: C25792
    Datasheet: https://atta.szlcsc.com/upload/public/pdf/source/20200306/C422600_1E6D84923E4A46A82E41ADD87F860B5C.pdf
  schematic_page: P2
  function_block: SD_DETECT pull-up
  schematic_notes:
  - 47k pull-up on SD_DETECT card-detect signal
- designator: R4
  type: resistor
  value: 33kΩ
  footprint: R0402
  comment: 33kΩ
  manufacturer: UNI-ROYAL(厚声)
  manufacturer_part: 0402WGF3302TCE
  supplier_part: C25779
  placement:
    x_mm: 57.023
    y_mm: 74.803
    rotation_deg: 270.0
    layer: T
  pins:
    '1': GND
    '2': VFB
  bom_data:
    No.: '32'
    Designator: R4
    Quantity: '1'
    Manufacturer: UNI-ROYAL(厚声)
    Manufacturer Part: 0402WGF3302TCE
    Comment: 33kΩ
    Footprint: R0402
    Mounting Style: SMT
    Supplier Part: C25779
  schematic_page: P1
  function_block: Buck converter feedback divider lower resistor
  schematic_notes:
  - 33k lower resistor of VFB divider for TLV62569 U4
  - 'With R10=150k: Vout = 0.6V * (1 + 150k/33k) = 3.33V'
- designator: R5
  type: resistor
  value: 33Ω
  footprint: R0402
  comment: 33Ω
  manufacturer: UNI-ROYAL(厚声)
  manufacturer_part: 0402WGF330JTCE
  supplier_part: C25105
  placement:
    x_mm: 16.078
    y_mm: 70.866
    rotation_deg: 0.0
    layer: T
  pins:
    '1': CAN_RX
    '2': CAN_RX_INT
  bom_data:
    No.: '30'
    Designator: R1,R5,R13,R19,R26
    Quantity: '5'
    Manufacturer: UNI-ROYAL(厚声)
    Manufacturer Part: 0402WGF330JTCE
    Comment: 33Ω
    Footprint: R0402
    Mounting Style: SMT
    Supplier Part: C25105
    Datasheet: https://atta.szlcsc.com/upload/public/pdf/source/20200306/C422600_1E6D84923E4A46A82E41ADD87F860B5C.pdf
  schematic_page: P3
  function_block: CAN_RX series termination
  schematic_notes:
  - 33 ohm series resistor on CAN_RX from U3 transceiver to MCU
- designator: R6
  type: resistor
  value: 47kΩ
  footprint: R0402
  comment: 47kΩ
  manufacturer: UNI-ROYAL(厚声)
  manufacturer_part: 0402WGF4702TCE
  supplier_part: C25792
  placement:
    x_mm: 39.37
    y_mm: 71.882
    rotation_deg: 0.0
    layer: T
  pins:
    '1': SD_CS
    '2': 3.3V
  bom_data:
    No.: '31'
    Designator: R2,R3,R6,R7,R8,R41
    Quantity: '6'
    Manufacturer: UNI-ROYAL(厚声)
    Manufacturer Part: 0402WGF4702TCE
    Comment: 47kΩ
    Footprint: R0402
    Mounting Style: SMT
    Supplier Part: C25792
    Datasheet: https://atta.szlcsc.com/upload/public/pdf/source/20200306/C422600_1E6D84923E4A46A82E41ADD87F860B5C.pdf
  schematic_page: P2
  function_block: SD_CS pull-up
  schematic_notes:
  - 47k pull-up on SD_CS; keeps SD card deselected at startup
- designator: R7
  type: resistor
  value: 47kΩ
  footprint: R0402
  comment: 47kΩ
  manufacturer: UNI-ROYAL(厚声)
  manufacturer_part: 0402WGF4702TCE
  supplier_part: C25792
  placement:
    x_mm: 41.402
    y_mm: 73.914
    rotation_deg: 0.0
    layer: T
  pins:
    '1': SPI2_MOSI
    '2': 3.3V
  bom_data:
    No.: '31'
    Designator: R2,R3,R6,R7,R8,R41
    Quantity: '6'
    Manufacturer: UNI-ROYAL(厚声)
    Manufacturer Part: 0402WGF4702TCE
    Comment: 47kΩ
    Footprint: R0402
    Mounting Style: SMT
    Supplier Part: C25792
    Datasheet: https://atta.szlcsc.com/upload/public/pdf/source/20200306/C422600_1E6D84923E4A46A82E41ADD87F860B5C.pdf
  schematic_page: P2
  function_block: SPI2_MOSI pull-up
  schematic_notes:
  - 47k pull-up on SPI2_MOSI
- designator: R8
  type: resistor
  value: 47kΩ
  footprint: R0402
  comment: 47kΩ
  manufacturer: UNI-ROYAL(厚声)
  manufacturer_part: 0402WGF4702TCE
  supplier_part: C25792
  placement:
    x_mm: 45.72
    y_mm: 75.946
    rotation_deg: 0.0
    layer: T
  pins:
    '1': SPI2_MISO
    '2': 3.3V
  bom_data:
    No.: '31'
    Designator: R2,R3,R6,R7,R8,R41
    Quantity: '6'
    Manufacturer: UNI-ROYAL(厚声)
    Manufacturer Part: 0402WGF4702TCE
    Comment: 47kΩ
    Footprint: R0402
    Mounting Style: SMT
    Supplier Part: C25792
    Datasheet: https://atta.szlcsc.com/upload/public/pdf/source/20200306/C422600_1E6D84923E4A46A82E41ADD87F860B5C.pdf
  schematic_page: P2
  function_block: SPI2_MISO pull-up
  schematic_notes:
  - 47k pull-up on SPI2_MISO
- designator: R9
  type: resistor
  value: 10kΩ
  footprint: R0402
  comment: 10kΩ
  manufacturer: UNI-ROYAL(厚声)
  manufacturer_part: 0402WGF1002TCE
  supplier_part: C25744
  placement:
    x_mm: 46.609
    y_mm: 71.882
    rotation_deg: 0.0
    layer: T
  pins:
    '1': 3.3V
    '2': FLASH_CS
  bom_data:
    No.: '33'
    Designator: R9,R11,R12,R16,R18,R23,R39,R42,R43,R44,R45,R46
    Quantity: '12'
    Manufacturer: UNI-ROYAL(厚声)
    Manufacturer Part: 0402WGF1002TCE
    Comment: 10kΩ
    Footprint: R0402
    Mounting Style: SMT
    Supplier Part: C25744
    Datasheet: https://atta.szlcsc.com/upload/public/pdf/source/20200306/C422600_1E6D84923E4A46A82E41ADD87F860B5C.pdf,https://item.szlcsc.com/datasheet/0402WGF1002TCE/26487.html
  schematic_page: P2
  function_block: SPI flash CS pull-up
  schematic_notes:
  - 10k pull-up on FLASH_CS; keeps SPI flash U6 deselected at startup
- designator: R10
  type: resistor
  value: 150kΩ
  footprint: R0402
  comment: 150kΩ
  manufacturer: UNI-ROYAL(厚声)
  manufacturer_part: 0402WGF1503TCE
  supplier_part: C25755
  placement:
    x_mm: 57.023
    y_mm: 71.501
    rotation_deg: 270.0
    layer: T
  pins:
    '1': VFB
    '2': 3.3V
  bom_data:
    No.: '34'
    Designator: R10
    Quantity: '1'
    Manufacturer: UNI-ROYAL(厚声)
    Manufacturer Part: 0402WGF1503TCE
    Comment: 150kΩ
    Footprint: R0402
    Mounting Style: SMT
    Supplier Part: C25755
    Datasheet: https://atta.szlcsc.com/upload/public/pdf/source/20200306/C422600_1E6D84923E4A46A82E41ADD87F860B5C.pdf
  schematic_page: P1
  function_block: Buck converter feedback divider upper resistor
  schematic_notes:
  - 150k upper resistor of VFB divider for TLV62569 U4
  - C9 22pF in parallel for feed-forward phase compensation
- designator: R11
  type: resistor
  value: 10kΩ
  footprint: R0402
  comment: 10kΩ
  manufacturer: UNI-ROYAL(厚声)
  manufacturer_part: 0402WGF1002TCE
  supplier_part: C25744
  placement:
    x_mm: 16.51
    y_mm: 67.183
    rotation_deg: 90.0
    layer: T
  pins:
    '1': IRQ_I2C
    '2': 3.3V
  bom_data:
    No.: '33'
    Designator: R9,R11,R12,R16,R18,R23,R39,R42,R43,R44,R45,R46
    Quantity: '12'
    Manufacturer: UNI-ROYAL(厚声)
    Manufacturer Part: 0402WGF1002TCE
    Comment: 10kΩ
    Footprint: R0402
    Mounting Style: SMT
    Supplier Part: C25744
    Datasheet: https://atta.szlcsc.com/upload/public/pdf/source/20200306/C422600_1E6D84923E4A46A82E41ADD87F860B5C.pdf,https://item.szlcsc.com/datasheet/0402WGF1002TCE/26487.html
  schematic_page: P2
  function_block: IRQ_I2C pull-up
  schematic_notes:
  - 10k pull-up on IRQ_I2C interrupt output from RTC U5
- designator: R12
  type: resistor
  value: 10kΩ
  footprint: R0402
  comment: 10kΩ
  manufacturer: UNI-ROYAL(厚声)
  manufacturer_part: 0402WGF1002TCE
  supplier_part: C25744
  placement:
    x_mm: 21.082
    y_mm: 67.056
    rotation_deg: 90.0
    layer: T
  pins:
    '1': RTC
    '2': 3.3V
  bom_data:
    No.: '33'
    Designator: R9,R11,R12,R16,R18,R23,R39,R42,R43,R44,R45,R46
    Quantity: '12'
    Manufacturer: UNI-ROYAL(厚声)
    Manufacturer Part: 0402WGF1002TCE
    Comment: 10kΩ
    Footprint: R0402
    Mounting Style: SMT
    Supplier Part: C25744
    Datasheet: https://atta.szlcsc.com/upload/public/pdf/source/20200306/C422600_1E6D84923E4A46A82E41ADD87F860B5C.pdf,https://item.szlcsc.com/datasheet/0402WGF1002TCE/26487.html
  schematic_page: P2
  function_block: RTC frequency output pull-up
  schematic_notes:
  - 10k pull-up on RTC FREQ/INT output from U5
- designator: R13
  type: resistor
  value: 33Ω
  footprint: R0402
  comment: 33Ω
  manufacturer: UNI-ROYAL(厚声)
  manufacturer_part: 0402WGF330JTCE
  supplier_part: C25105
  placement:
    x_mm: 44.958
    y_mm: 69.85
    rotation_deg: 180.0
    layer: T
  pins:
    '1': SPI2_MISO
    '2': $2N741099
  bom_data:
    No.: '30'
    Designator: R1,R5,R13,R19,R26
    Quantity: '5'
    Manufacturer: UNI-ROYAL(厚声)
    Manufacturer Part: 0402WGF330JTCE
    Comment: 33Ω
    Footprint: R0402
    Mounting Style: SMT
    Supplier Part: C25105
    Datasheet: https://atta.szlcsc.com/upload/public/pdf/source/20200306/C422600_1E6D84923E4A46A82E41ADD87F860B5C.pdf
  schematic_page: P2
  function_block: SPI flash MISO series termination
  schematic_notes:
  - 33 ohm series termination on SPI2_MISO from SPI flash U6
- designator: R14
  type: resistor
  value: 910kΩ
  footprint: R0402
  comment: 910kΩ
  manufacturer: UNI-ROYAL(厚声)
  manufacturer_part: 0402WGF9103TCE
  supplier_part: C25800
  placement:
    x_mm: 30.48
    y_mm: 65.405
    rotation_deg: 180.0
    layer: T
  pins:
    '1': GND
    '2': IREF
  bom_data:
    No.: '35'
    Designator: R14
    Quantity: '1'
    Manufacturer: UNI-ROYAL(厚声)
    Manufacturer Part: 0402WGF9103TCE
    Comment: 910kΩ
    Footprint: R0402
    Mounting Style: SMT
    Supplier Part: C25800
    Datasheet: https://atta.szlcsc.com/upload/public/pdf/source/20200306/C422600_1E6D84923E4A46A82E41ADD87F860B5C.pdf
  schematic_page: P2
  function_block: OLED IREF current reference resistor
  schematic_notes:
  - 910k resistor from IREF pin of FPC1 to GND
  - Sets display current reference for OLED driver
  alternate_parts:
  - supplier_part: C25800
    manufacturer_part: 0402 910k 1%
    note: 'Primary: 1% tolerance'
  - supplier_part: C11866
    manufacturer_part: 0402 910k 5%
    note: 'Alternate: 5% tolerance'
- designator: R15
  type: resistor
  value: 4.7kΩ
  footprint: R0402
  comment: 4.7kΩ
  manufacturer: UNI-ROYAL(厚声)
  manufacturer_part: 0402WGF4701TCE
  supplier_part: C25900
  placement:
    x_mm: 21.209
    y_mm: 56.769
    rotation_deg: 180.0
    layer: T
  pins:
    '1': 3.3V
    '2': I2C1_SCL
  bom_data:
    No.: '36'
    Designator: R15,R17,R20,R21,R40
    Quantity: '5'
    Manufacturer: UNI-ROYAL(厚声)
    Manufacturer Part: 0402WGF4701TCE
    Comment: 4.7kΩ
    Footprint: R0402
    Mounting Style: SMT
    Supplier Part: C25900
    Datasheet: https://atta.szlcsc.com/upload/public/pdf/source/20200306/C422600_1E6D84923E4A46A82E41ADD87F860B5C.pdf
  schematic_page: P2
  function_block: I2C1_SCL pull-up
  schematic_notes:
  - 4.7k pull-up on I2C1_SCL bus
- designator: R16
  type: resistor
  value: 10kΩ
  footprint: R0402
  comment: 10kΩ
  manufacturer: UNI-ROYAL(厚声)
  manufacturer_part: 0402WGF1002TCE
  supplier_part: C25744
  placement:
    x_mm: 13.335
    y_mm: 51.308
    rotation_deg: 180.0
    layer: T
  pins:
    '1': CAN_TX
    '2': 3.3V
  bom_data:
    No.: '33'
    Designator: R9,R11,R12,R16,R18,R23,R39,R42,R43,R44,R45,R46
    Quantity: '12'
    Manufacturer: UNI-ROYAL(厚声)
    Manufacturer Part: 0402WGF1002TCE
    Comment: 10kΩ
    Footprint: R0402
    Mounting Style: SMT
    Supplier Part: C25744
    Datasheet: https://atta.szlcsc.com/upload/public/pdf/source/20200306/C422600_1E6D84923E4A46A82E41ADD87F860B5C.pdf,https://item.szlcsc.com/datasheet/0402WGF1002TCE/26487.html
  schematic_page: P3
  function_block: CAN_TX pull-up
  schematic_notes:
  - 10k pull-up on CAN_TX; keeps CAN bus recessive at startup
- designator: R17
  type: resistor
  value: 4.7kΩ
  footprint: R0402
  comment: 4.7kΩ
  manufacturer: UNI-ROYAL(厚声)
  manufacturer_part: 0402WGF4701TCE
  supplier_part: C25900
  placement:
    x_mm: 17.018
    y_mm: 50.927
    rotation_deg: 0.0
    layer: T
  pins:
    '1': 3.3V
    '2': I2C1_SDA
  bom_data:
    No.: '36'
    Designator: R15,R17,R20,R21,R40
    Quantity: '5'
    Manufacturer: UNI-ROYAL(厚声)
    Manufacturer Part: 0402WGF4701TCE
    Comment: 4.7kΩ
    Footprint: R0402
    Mounting Style: SMT
    Supplier Part: C25900
    Datasheet: https://atta.szlcsc.com/upload/public/pdf/source/20200306/C422600_1E6D84923E4A46A82E41ADD87F860B5C.pdf
  schematic_page: P2
  function_block: I2C1_SDA pull-up
  schematic_notes:
  - 4.7k pull-up on I2C1_SDA bus
- designator: R18
  type: resistor
  value: 10kΩ
  footprint: R0402
  comment: 10kΩ
  manufacturer: UNI-ROYAL(厚声)
  manufacturer_part: 0402WGF1002TCE
  supplier_part: C25744
  placement:
    x_mm: 37.287
    y_mm: 52.832
    rotation_deg: 0.0
    layer: T
  pins:
    '1': 3.3V
    '2': QSPI1_CS
  bom_data:
    No.: '33'
    Designator: R9,R11,R12,R16,R18,R23,R39,R42,R43,R44,R45,R46
    Quantity: '12'
    Manufacturer: UNI-ROYAL(厚声)
    Manufacturer Part: 0402WGF1002TCE
    Comment: 10kΩ
    Footprint: R0402
    Mounting Style: SMT
    Supplier Part: C25744
    Datasheet: https://atta.szlcsc.com/upload/public/pdf/source/20200306/C422600_1E6D84923E4A46A82E41ADD87F860B5C.pdf,https://item.szlcsc.com/datasheet/0402WGF1002TCE/26487.html
  schematic_page: P1
  function_block: QSPI1_CS pull-up
  schematic_notes:
  - 10k pull-up on QSPI1_CS; keeps QSPI flash U8 deselected at startup
- designator: R19
  type: resistor
  value: 33Ω
  footprint: R0402
  comment: 33Ω
  manufacturer: UNI-ROYAL(厚声)
  manufacturer_part: 0402WGF330JTCE
  supplier_part: C25105
  placement:
    x_mm: 26.035
    y_mm: 47.498
    rotation_deg: 180.0
    layer: T
  pins:
    '1': $1N200184
    '2': CAN_TX
  bom_data:
    No.: '30'
    Designator: R1,R5,R13,R19,R26
    Quantity: '5'
    Manufacturer: UNI-ROYAL(厚声)
    Manufacturer Part: 0402WGF330JTCE
    Comment: 33Ω
    Footprint: R0402
    Mounting Style: SMT
    Supplier Part: C25105
    Datasheet: https://atta.szlcsc.com/upload/public/pdf/source/20200306/C422600_1E6D84923E4A46A82E41ADD87F860B5C.pdf
  schematic_page: P1
  function_block: CAN_TX series termination
  schematic_notes:
  - 33 ohm series resistor on CAN_TX from MCU to CAN transceiver U3
- designator: R20
  type: resistor
  value: 4.7kΩ
  footprint: R0402
  comment: 4.7kΩ
  manufacturer: UNI-ROYAL(厚声)
  manufacturer_part: 0402WGF4701TCE
  supplier_part: C25900
  placement:
    x_mm: 8.382
    y_mm: 39.624
    rotation_deg: 0.0
    layer: T
  pins:
    '1': 3.3V
    '2': I2C3_SCL
  bom_data:
    No.: '36'
    Designator: R15,R17,R20,R21,R40
    Quantity: '5'
    Manufacturer: UNI-ROYAL(厚声)
    Manufacturer Part: 0402WGF4701TCE
    Comment: 4.7kΩ
    Footprint: R0402
    Mounting Style: SMT
    Supplier Part: C25900
    Datasheet: https://atta.szlcsc.com/upload/public/pdf/source/20200306/C422600_1E6D84923E4A46A82E41ADD87F860B5C.pdf
  schematic_page: P2
  function_block: I2C3_SCL pull-up
  schematic_notes:
  - 4.7k pull-up on I2C3_SCL bus
- designator: R21
  type: resistor
  value: 4.7kΩ
  footprint: R0402
  comment: 4.7kΩ
  manufacturer: UNI-ROYAL(厚声)
  manufacturer_part: 0402WGF4701TCE
  supplier_part: C25900
  placement:
    x_mm: 9.906
    y_mm: 37.973
    rotation_deg: 0.0
    layer: T
  pins:
    '1': 3.3V
    '2': I2C3_SDA
  bom_data:
    No.: '36'
    Designator: R15,R17,R20,R21,R40
    Quantity: '5'
    Manufacturer: UNI-ROYAL(厚声)
    Manufacturer Part: 0402WGF4701TCE
    Comment: 4.7kΩ
    Footprint: R0402
    Mounting Style: SMT
    Supplier Part: C25900
    Datasheet: https://atta.szlcsc.com/upload/public/pdf/source/20200306/C422600_1E6D84923E4A46A82E41ADD87F860B5C.pdf
  schematic_page: P2
  function_block: I2C3_SDA pull-up
  schematic_notes:
  - 4.7k pull-up on I2C3_SDA bus
- designator: R22
  type: resistor
  value: 5.1kΩ
  footprint: R0402
  comment: 5.1kΩ
  manufacturer: UNI-ROYAL(厚声)
  manufacturer_part: 0402WGF5101TCE
  supplier_part: C25905
  placement:
    x_mm: 48.641
    y_mm: 36.957
    rotation_deg: 180.0
    layer: T
  pins:
    '1': $1N254528
    '2': GND
  bom_data:
    No.: '37'
    Designator: R22,R25
    Quantity: '2'
    Manufacturer: UNI-ROYAL(厚声)
    Manufacturer Part: 0402WGF5101TCE
    Comment: 5.1kΩ
    Footprint: R0402
    Mounting Style: SMT
    Supplier Part: C25905
  schematic_page: P1
  function_block: USB-C CC2 pull-down
  schematic_notes:
  - 5.1k pull-down on CC2 (USB-C pin B5) for USB sink current advertisement
  - Required for USB-C power delivery negotiation
- designator: R23
  type: resistor
  value: 10kΩ
  footprint: R0402
  comment: 10kΩ
  manufacturer: UNI-ROYAL(厚声)
  manufacturer_part: 0402WGF1002TCE
  supplier_part: C25744
  placement:
    x_mm: 7.493
    y_mm: 32.639
    rotation_deg: 270.0
    layer: T
  pins:
    '1': BOOT0
    '2': GND
  bom_data:
    No.: '33'
    Designator: R9,R11,R12,R16,R18,R23,R39,R42,R43,R44,R45,R46
    Quantity: '12'
    Manufacturer: UNI-ROYAL(厚声)
    Manufacturer Part: 0402WGF1002TCE
    Comment: 10kΩ
    Footprint: R0402
    Mounting Style: SMT
    Supplier Part: C25744
    Datasheet: https://atta.szlcsc.com/upload/public/pdf/source/20200306/C422600_1E6D84923E4A46A82E41ADD87F860B5C.pdf,https://item.szlcsc.com/datasheet/0402WGF1002TCE/26487.html
  schematic_page: P1
  function_block: BOOT0 pull-down
  schematic_notes:
  - 10k pull-down on BOOT0; holds MCU in normal boot mode at power-up
- designator: R24
  type: resistor
  value: 12kΩ
  footprint: R0402
  comment: 12kΩ
  manufacturer: UNI-ROYAL(厚声)
  manufacturer_part: 0402WGF1202TCE
  supplier_part: C25752
  placement:
    x_mm: 36.678
    y_mm: 34.341
    rotation_deg: 270.0
    layer: T
  pins:
    '1': HS_R
    '2': GND
  bom_data:
    No.: '38'
    Designator: R24
    Quantity: '1'
    Manufacturer: UNI-ROYAL(厚声)
    Manufacturer Part: 0402WGF1202TCE
    Comment: 12kΩ
    Footprint: R0402
    Mounting Style: SMT
    Supplier Part: C25752
    Datasheet: https://atta.szlcsc.com/upload/public/pdf/source/20200306/C422600_1E6D84923E4A46A82E41ADD87F860B5C.pdf
  schematic_page: P1
  function_block: USB HS PHY termination resistor
  schematic_notes:
  - 12k 1% precision resistor on HS_R pin for AT32 USB high-speed PHY
  - 1% tolerance required for USB HS eye diagram compliance
- designator: R25
  type: resistor
  value: 5.1kΩ
  footprint: R0402
  comment: 5.1kΩ
  manufacturer: UNI-ROYAL(厚声)
  manufacturer_part: 0402WGF5101TCE
  supplier_part: C25905
  placement:
    x_mm: 48.641
    y_mm: 33.934
    rotation_deg: 0.0
    layer: T
  pins:
    '1': GND
    '2': $1N254529
  bom_data:
    No.: '37'
    Designator: R22,R25
    Quantity: '2'
    Manufacturer: UNI-ROYAL(厚声)
    Manufacturer Part: 0402WGF5101TCE
    Comment: 5.1kΩ
    Footprint: R0402
    Mounting Style: SMT
    Supplier Part: C25905
  schematic_page: P1
  function_block: USB-C CC1 pull-down
  schematic_notes:
  - 5.1k pull-down on CC1 (USB-C pin A5) for USB sink detection
- designator: R26
  type: resistor
  value: 33Ω
  footprint: R0402
  comment: 33Ω
  manufacturer: UNI-ROYAL(厚声)
  manufacturer_part: 0402WGF330JTCE
  supplier_part: C25105
  placement:
    x_mm: 36.957
    y_mm: 30.861
    rotation_deg: 315.0
    layer: T
  pins:
    '1': T_RST_OUT
    '2': $3N5450
  bom_data:
    No.: '30'
    Designator: R1,R5,R13,R19,R26
    Quantity: '5'
    Manufacturer: UNI-ROYAL(厚声)
    Manufacturer Part: 0402WGF330JTCE
    Comment: 33Ω
    Footprint: R0402
    Mounting Style: SMT
    Supplier Part: C25105
    Datasheet: https://atta.szlcsc.com/upload/public/pdf/source/20200306/C422600_1E6D84923E4A46A82E41ADD87F860B5C.pdf
  schematic_page: P3
  function_block: Target reset MOSFET gate series resistor
  schematic_notes:
  - 33 ohm series resistor between MCU T_RST_OUT and Q1 gate
- designator: R27
  type: resistor
  value: 1MΩ
  footprint: R0402
  comment: 1MΩ
  manufacturer: UNI-ROYAL(厚声)
  manufacturer_part: 0402WGF1004TCE
  supplier_part: C26083
  placement:
    x_mm: 48.768
    y_mm: 29.21
    rotation_deg: 0.0
    layer: T
  pins:
    '1': GND
    '2': $1N254540
  bom_data:
    No.: '39'
    Designator: R27
    Quantity: '1'
    Manufacturer: UNI-ROYAL(厚声)
    Manufacturer Part: 0402WGF1004TCE
    Comment: 1MΩ
    Footprint: R0402
    Mounting Style: SMT
    Supplier Part: C26083
    Datasheet: https://atta.szlcsc.com/upload/public/pdf/source/20200306/C422600_1E6D84923E4A46A82E41ADD87F860B5C.pdf
  schematic_page: P1
  function_block: USB-C shield resistor
  schematic_notes:
  - 1M resistor from USB-C connector shell pin to GND
  - Provides ESD discharge path while limiting leakage current
- designator: R28
  type: resistor
  value: 100kΩ
  footprint: R0402
  comment: 100kΩ
  manufacturer: UNI-ROYAL(厚声)
  manufacturer_part: 0402WGF1003TCE
  supplier_part: C25741
  placement:
    x_mm: 21.336
    y_mm: 19.177
    rotation_deg: 0.0
    layer: T
  pins:
    '1': $3N4349
    '2': VIO
  bom_data:
    No.: '40'
    Designator: R28,R32,R33,R34,R35,R36,R37
    Quantity: '7'
    Manufacturer: UNI-ROYAL(厚声)
    Manufacturer Part: 0402WGF1003TCE
    Comment: 100kΩ
    Footprint: R0402
    Mounting Style: SMT
    Supplier Part: C25741
    Datasheet: https://atta.szlcsc.com/upload/public/pdf/source/20200306/C422600_1E6D84923E4A46A82E41ADD87F860B5C.pdf
  schematic_page: P3
  function_block: Target interface VIO pull-up
  schematic_notes:
  - 100k pull-up on U13 level-translator B-side output to VIO
- designator: R29
  type: resistor
  value: 22kΩ
  footprint: R0402
  comment: 22kΩ
  manufacturer: UNI-ROYAL(厚声)
  manufacturer_part: 0402WGF2202TCE
  supplier_part: C25768
  placement:
    x_mm: 28.448
    y_mm: 21.336
    rotation_deg: 0.0
    layer: T
  pins:
    '1': $2N788718
    '2': $2N788708
  bom_data:
    No.: '41'
    Designator: R29,R30,R31
    Quantity: '3'
    Manufacturer: UNI-ROYAL(厚声)
    Manufacturer Part: 0402WGF2202TCE
    Comment: 22kΩ
    Footprint: R0402
    Mounting Style: SMT
    Supplier Part: C25768
    Datasheet: https://atta.szlcsc.com/upload/public/pdf/source/20200306/C422600_1E6D84923E4A46A82E41ADD87F860B5C.pdf
  schematic_page: P2
  function_block: SW_NEXT debounce resistor
  schematic_notes:
  - 22k series resistor forming RC debounce with C39 1uF for SW_NEXT
- designator: R30
  type: resistor
  value: 22kΩ
  footprint: R0402
  comment: 22kΩ
  manufacturer: UNI-ROYAL(厚声)
  manufacturer_part: 0402WGF2202TCE
  supplier_part: C25768
  placement:
    x_mm: 30.988
    y_mm: 21.336
    rotation_deg: 0.0
    layer: T
  pins:
    '1': $2N788825
    '2': $2N788818
  bom_data:
    No.: '41'
    Designator: R29,R30,R31
    Quantity: '3'
    Manufacturer: UNI-ROYAL(厚声)
    Manufacturer Part: 0402WGF2202TCE
    Comment: 22kΩ
    Footprint: R0402
    Mounting Style: SMT
    Supplier Part: C25768
    Datasheet: https://atta.szlcsc.com/upload/public/pdf/source/20200306/C422600_1E6D84923E4A46A82E41ADD87F860B5C.pdf
  schematic_page: P2
  function_block: SW_SELECT debounce resistor
  schematic_notes:
  - 22k series resistor forming RC debounce with C40 1uF for SW_SELECT
- designator: R31
  type: resistor
  value: 22kΩ
  footprint: R0402
  comment: 22kΩ
  manufacturer: UNI-ROYAL(厚声)
  manufacturer_part: 0402WGF2202TCE
  supplier_part: C25768
  placement:
    x_mm: 33.528
    y_mm: 21.336
    rotation_deg: 0.0
    layer: T
  pins:
    '1': $2N788929
    '2': $2N788938
  bom_data:
    No.: '41'
    Designator: R29,R30,R31
    Quantity: '3'
    Manufacturer: UNI-ROYAL(厚声)
    Manufacturer Part: 0402WGF2202TCE
    Comment: 22kΩ
    Footprint: R0402
    Mounting Style: SMT
    Supplier Part: C25768
    Datasheet: https://atta.szlcsc.com/upload/public/pdf/source/20200306/C422600_1E6D84923E4A46A82E41ADD87F860B5C.pdf
  schematic_page: P2
  function_block: SW_PREV debounce resistor
  schematic_notes:
  - 22k series resistor forming RC debounce with C41 1uF for SW_PREV
- designator: R32
  type: resistor
  value: 100kΩ
  footprint: R0402
  comment: 100kΩ
  manufacturer: UNI-ROYAL(厚声)
  manufacturer_part: 0402WGF1003TCE
  supplier_part: C25741
  placement:
    x_mm: 12.7
    y_mm: 17.653
    rotation_deg: 180.0
    layer: T
  pins:
    '1': $3N4347
    '2': VIO
  bom_data:
    No.: '40'
    Designator: R28,R32,R33,R34,R35,R36,R37
    Quantity: '7'
    Manufacturer: UNI-ROYAL(厚声)
    Manufacturer Part: 0402WGF1003TCE
    Comment: 100kΩ
    Footprint: R0402
    Mounting Style: SMT
    Supplier Part: C25741
    Datasheet: https://atta.szlcsc.com/upload/public/pdf/source/20200306/C422600_1E6D84923E4A46A82E41ADD87F860B5C.pdf
  schematic_page: P3
  function_block: Target interface VIO pull-up
  schematic_notes:
  - 100k pull-up on U13 level-translator B-side output to VIO
- designator: R33
  type: resistor
  value: 100kΩ
  footprint: R0402
  comment: 100kΩ
  manufacturer: UNI-ROYAL(厚声)
  manufacturer_part: 0402WGF1003TCE
  supplier_part: C25741
  placement:
    x_mm: 12.7
    y_mm: 16.129
    rotation_deg: 180.0
    layer: T
  pins:
    '1': $3N4348
    '2': VIO
  bom_data:
    No.: '40'
    Designator: R28,R32,R33,R34,R35,R36,R37
    Quantity: '7'
    Manufacturer: UNI-ROYAL(厚声)
    Manufacturer Part: 0402WGF1003TCE
    Comment: 100kΩ
    Footprint: R0402
    Mounting Style: SMT
    Supplier Part: C25741
    Datasheet: https://atta.szlcsc.com/upload/public/pdf/source/20200306/C422600_1E6D84923E4A46A82E41ADD87F860B5C.pdf
  schematic_page: P3
  function_block: Target interface VIO pull-up
  schematic_notes:
  - 100k pull-up on U13 level-translator B-side output to VIO
- designator: R34
  type: resistor
  value: 100kΩ
  footprint: R0402
  comment: 100kΩ
  manufacturer: UNI-ROYAL(厚声)
  manufacturer_part: 0402WGF1003TCE
  supplier_part: C25741
  placement:
    x_mm: 21.336
    y_mm: 17.653
    rotation_deg: 0.0
    layer: T
  pins:
    '1': $3N4350
    '2': VIO
  bom_data:
    No.: '40'
    Designator: R28,R32,R33,R34,R35,R36,R37
    Quantity: '7'
    Manufacturer: UNI-ROYAL(厚声)
    Manufacturer Part: 0402WGF1003TCE
    Comment: 100kΩ
    Footprint: R0402
    Mounting Style: SMT
    Supplier Part: C25741
    Datasheet: https://atta.szlcsc.com/upload/public/pdf/source/20200306/C422600_1E6D84923E4A46A82E41ADD87F860B5C.pdf
  schematic_page: P3
  function_block: Target interface VIO pull-up
  schematic_notes:
  - 100k pull-up on U13 level-translator B-side output to VIO
- designator: R35
  type: resistor
  value: 100kΩ
  footprint: R0402
  comment: 100kΩ
  manufacturer: UNI-ROYAL(厚声)
  manufacturer_part: 0402WGF1003TCE
  supplier_part: C25741
  placement:
    x_mm: 39.624
    y_mm: 16.129
    rotation_deg: 180.0
    layer: T
  pins:
    '1': $3N5228
    '2': VIO
  bom_data:
    No.: '40'
    Designator: R28,R32,R33,R34,R35,R36,R37
    Quantity: '7'
    Manufacturer: UNI-ROYAL(厚声)
    Manufacturer Part: 0402WGF1003TCE
    Comment: 100kΩ
    Footprint: R0402
    Mounting Style: SMT
    Supplier Part: C25741
    Datasheet: https://atta.szlcsc.com/upload/public/pdf/source/20200306/C422600_1E6D84923E4A46A82E41ADD87F860B5C.pdf
  schematic_page: P3
  function_block: Target AUX interface VIO pull-up
  schematic_notes:
  - 100k pull-up on U15 level-translator B-side output to VIO
- designator: R36
  type: resistor
  value: 100kΩ
  footprint: R0402
  comment: 100kΩ
  manufacturer: UNI-ROYAL(厚声)
  manufacturer_part: 0402WGF1003TCE
  supplier_part: C25741
  placement:
    x_mm: 39.624
    y_mm: 17.653
    rotation_deg: 180.0
    layer: T
  pins:
    '1': $3N5229
    '2': VIO
  bom_data:
    No.: '40'
    Designator: R28,R32,R33,R34,R35,R36,R37
    Quantity: '7'
    Manufacturer: UNI-ROYAL(厚声)
    Manufacturer Part: 0402WGF1003TCE
    Comment: 100kΩ
    Footprint: R0402
    Mounting Style: SMT
    Supplier Part: C25741
    Datasheet: https://atta.szlcsc.com/upload/public/pdf/source/20200306/C422600_1E6D84923E4A46A82E41ADD87F860B5C.pdf
  schematic_page: P3
  function_block: Target AUX interface VIO pull-up
  schematic_notes:
  - 100k pull-up on U15 level-translator B-side output to VIO
- designator: R37
  type: resistor
  value: 100kΩ
  footprint: R0402
  comment: 100kΩ
  manufacturer: UNI-ROYAL(厚声)
  manufacturer_part: 0402WGF1003TCE
  supplier_part: C25741
  placement:
    x_mm: 49.911
    y_mm: 16.891
    rotation_deg: 90.0
    layer: T
  pins:
    '1': GND
    '2': $3N5450
  bom_data:
    No.: '40'
    Designator: R28,R32,R33,R34,R35,R36,R37
    Quantity: '7'
    Manufacturer: UNI-ROYAL(厚声)
    Manufacturer Part: 0402WGF1003TCE
    Comment: 100kΩ
    Footprint: R0402
    Mounting Style: SMT
    Supplier Part: C25741
    Datasheet: https://atta.szlcsc.com/upload/public/pdf/source/20200306/C422600_1E6D84923E4A46A82E41ADD87F860B5C.pdf
  schematic_page: P3
  function_block: Target RST pull-up to VIO
  schematic_notes:
  - 100k pull-up from T_RST to VIO
  - Holds target reset line high (inactive) when Q1 is off
- designator: R38
  type: resistor
  value: 150Ω
  footprint: R0402
  comment: 150Ω
  manufacturer: UNI-ROYAL(厚声)
  manufacturer_part: 0402WGF1500TCE
  supplier_part: C25082
  placement:
    x_mm: 4.699
    y_mm: 13.589
    rotation_deg: 270.0
    layer: T
  pins:
    '1': LED0
    '2': $1N206167
  bom_data:
    No.: '42'
    Designator: R38
    Quantity: '1'
    Manufacturer: UNI-ROYAL(厚声)
    Manufacturer Part: 0402WGF1500TCE
    Comment: 150Ω
    Footprint: R0402
    Mounting Style: SMT
    Supplier Part: C25082
    Datasheet: https://atta.szlcsc.com/upload/public/pdf/source/20200306/C422600_1E6D84923E4A46A82E41ADD87F860B5C.pdf
  schematic_page: P1
  function_block: LED current limiter
  schematic_notes:
  - 150 ohm current limiter for status LED LED1; driven by MCU LED0 net
- designator: R39
  type: resistor
  value: 10kΩ
  footprint: R0402
  comment: 10kΩ
  manufacturer: UNI-ROYAL(厚声)
  manufacturer_part: 0402WGF1002TCE
  supplier_part: C25744
  placement:
    x_mm: 10.414
    y_mm: 11.43
    rotation_deg: 90.0
    layer: T
  pins:
    '1': GND
    '2': ADC_VIO
  bom_data:
    No.: '33'
    Designator: R9,R11,R12,R16,R18,R23,R39,R42,R43,R44,R45,R46
    Quantity: '12'
    Manufacturer: UNI-ROYAL(厚声)
    Manufacturer Part: 0402WGF1002TCE
    Comment: 10kΩ
    Footprint: R0402
    Mounting Style: SMT
    Supplier Part: C25744
    Datasheet: https://atta.szlcsc.com/upload/public/pdf/source/20200306/C422600_1E6D84923E4A46A82E41ADD87F860B5C.pdf,https://item.szlcsc.com/datasheet/0402WGF1002TCE/26487.html
  schematic_page: P3
  function_block: ADC_VIO voltage divider pull-down
  schematic_notes:
  - 10k resistor in ADC_VIO sense divider
  - MCU ADC reads VIO to determine target voltage for level translator direction control
- designator: R40
  type: resistor
  value: 4.7kΩ
  footprint: R0402
  comment: 4.7kΩ
  manufacturer: UNI-ROYAL(厚声)
  manufacturer_part: 0402WGF4701TCE
  supplier_part: C25900
  placement:
    x_mm: 11.938
    y_mm: 11.43
    rotation_deg: 270.0
    layer: T
  pins:
    '1': ADC_VIO
    '2': VIO
  bom_data:
    No.: '36'
    Designator: R15,R17,R20,R21,R40
    Quantity: '5'
    Manufacturer: UNI-ROYAL(厚声)
    Manufacturer Part: 0402WGF4701TCE
    Comment: 4.7kΩ
    Footprint: R0402
    Mounting Style: SMT
    Supplier Part: C25900
    Datasheet: https://atta.szlcsc.com/upload/public/pdf/source/20200306/C422600_1E6D84923E4A46A82E41ADD87F860B5C.pdf
  schematic_page: P3
  function_block: ADC_VIO voltage divider
  schematic_notes:
  - 4.7k resistor in ADC_VIO sense divider to VIO
- designator: R41
  type: resistor
  value: 47kΩ
  footprint: R0402
  comment: 47kΩ
  manufacturer: UNI-ROYAL(厚声)
  manufacturer_part: 0402WGF4702TCE
  supplier_part: C25792
  placement:
    x_mm: 24.638
    y_mm: 9.779
    rotation_deg: 0.0
    layer: T
  pins:
    '1': GND
    '2': T_POWER_ON
  bom_data:
    No.: '31'
    Designator: R2,R3,R6,R7,R8,R41
    Quantity: '6'
    Manufacturer: UNI-ROYAL(厚声)
    Manufacturer Part: 0402WGF4702TCE
    Comment: 47kΩ
    Footprint: R0402
    Mounting Style: SMT
    Supplier Part: C25792
    Datasheet: https://atta.szlcsc.com/upload/public/pdf/source/20200306/C422600_1E6D84923E4A46A82E41ADD87F860B5C.pdf
  schematic_page: P3
  function_block: Target power switch pull-down
  schematic_notes:
  - 47k pull-down on T_POWER_ON; target power off at startup
- designator: R42
  type: resistor
  value: 10kΩ
  footprint: R0402
  comment: 10kΩ
  manufacturer: UNI-ROYAL(厚声)
  manufacturer_part: 0402WGF1002TCE
  supplier_part: C25744
  placement:
    x_mm: 27.94
    y_mm: 11.176
    rotation_deg: 0.0
    layer: T
  pins:
    '1': SW_NEXT
    '2': 3.3V
  bom_data:
    No.: '33'
    Designator: R9,R11,R12,R16,R18,R23,R39,R42,R43,R44,R45,R46
    Quantity: '12'
    Manufacturer: UNI-ROYAL(厚声)
    Manufacturer Part: 0402WGF1002TCE
    Comment: 10kΩ
    Footprint: R0402
    Mounting Style: SMT
    Supplier Part: C25744
    Datasheet: https://atta.szlcsc.com/upload/public/pdf/source/20200306/C422600_1E6D84923E4A46A82E41ADD87F860B5C.pdf,https://item.szlcsc.com/datasheet/0402WGF1002TCE/26487.html
  schematic_page: P2
  function_block: SW_NEXT pull-up
  schematic_notes:
  - 10k pull-up on SW_NEXT encoder signal to 3.3V
- designator: R43
  type: resistor
  value: 10kΩ
  footprint: R0402
  comment: 10kΩ
  manufacturer: UNI-ROYAL(厚声)
  manufacturer_part: 0402WGF1002TCE
  supplier_part: C25744
  placement:
    x_mm: 30.48
    y_mm: 11.176
    rotation_deg: 0.0
    layer: T
  pins:
    '1': SW_SELECT
    '2': 3.3V
  bom_data:
    No.: '33'
    Designator: R9,R11,R12,R16,R18,R23,R39,R42,R43,R44,R45,R46
    Quantity: '12'
    Manufacturer: UNI-ROYAL(厚声)
    Manufacturer Part: 0402WGF1002TCE
    Comment: 10kΩ
    Footprint: R0402
    Mounting Style: SMT
    Supplier Part: C25744
    Datasheet: https://atta.szlcsc.com/upload/public/pdf/source/20200306/C422600_1E6D84923E4A46A82E41ADD87F860B5C.pdf,https://item.szlcsc.com/datasheet/0402WGF1002TCE/26487.html
  schematic_page: P2
  function_block: SW_SELECT pull-up
  schematic_notes:
  - 10k pull-up on SW_SELECT encoder signal to 3.3V
- designator: R44
  type: resistor
  value: 10kΩ
  footprint: R0402
  comment: 10kΩ
  manufacturer: UNI-ROYAL(厚声)
  manufacturer_part: 0402WGF1002TCE
  supplier_part: C25744
  placement:
    x_mm: 33.02
    y_mm: 11.176
    rotation_deg: 0.0
    layer: T
  pins:
    '1': SW_PREV
    '2': 3.3V
  bom_data:
    No.: '33'
    Designator: R9,R11,R12,R16,R18,R23,R39,R42,R43,R44,R45,R46
    Quantity: '12'
    Manufacturer: UNI-ROYAL(厚声)
    Manufacturer Part: 0402WGF1002TCE
    Comment: 10kΩ
    Footprint: R0402
    Mounting Style: SMT
    Supplier Part: C25744
    Datasheet: https://atta.szlcsc.com/upload/public/pdf/source/20200306/C422600_1E6D84923E4A46A82E41ADD87F860B5C.pdf,https://item.szlcsc.com/datasheet/0402WGF1002TCE/26487.html
  schematic_page: P2
  function_block: SW_PREV pull-up
  schematic_notes:
  - 10k pull-up on SW_PREV encoder signal to 3.3V
- designator: R45
  type: resistor
  value: 10kΩ
  footprint: R0402
  comment: 10kΩ
  manufacturer: UNI-ROYAL(厚声)
  manufacturer_part: 0402WGF1002TCE
  supplier_part: C25744
  placement:
    x_mm: 41.402
    y_mm: 11.43
    rotation_deg: 270.0
    layer: T
  pins:
    '1': T_OE
    '2': 3.3V
  bom_data:
    No.: '33'
    Designator: R9,R11,R12,R16,R18,R23,R39,R42,R43,R44,R45,R46
    Quantity: '12'
    Manufacturer: UNI-ROYAL(厚声)
    Manufacturer Part: 0402WGF1002TCE
    Comment: 10kΩ
    Footprint: R0402
    Mounting Style: SMT
    Supplier Part: C25744
    Datasheet: https://atta.szlcsc.com/upload/public/pdf/source/20200306/C422600_1E6D84923E4A46A82E41ADD87F860B5C.pdf,https://item.szlcsc.com/datasheet/0402WGF1002TCE/26487.html
  schematic_page: P3
  function_block: T_OE pull-up
  schematic_notes:
  - 10k pull-up on T_OE to 3.3V
  - Holds level translators U13 and U15 enabled (OE# active low) at startup
- designator: R46
  type: resistor
  value: 10kΩ
  footprint: R0402
  comment: 10kΩ
  manufacturer: UNI-ROYAL(厚声)
  manufacturer_part: 0402WGF1002TCE
  supplier_part: C25744
  placement:
    x_mm: 48.514
    y_mm: 11.43
    rotation_deg: 270.0
    layer: T
  pins:
    '1': VIO
    '2': T_RST
  bom_data:
    No.: '33'
    Designator: R9,R11,R12,R16,R18,R23,R39,R42,R43,R44,R45,R46
    Quantity: '12'
    Manufacturer: UNI-ROYAL(厚声)
    Manufacturer Part: 0402WGF1002TCE
    Comment: 10kΩ
    Footprint: R0402
    Mounting Style: SMT
    Supplier Part: C25744
    Datasheet: https://atta.szlcsc.com/upload/public/pdf/source/20200306/C422600_1E6D84923E4A46A82E41ADD87F860B5C.pdf,https://item.szlcsc.com/datasheet/0402WGF1002TCE/26487.html
  schematic_page: P3
  function_block: Target reset MOSFET gate pull-down
  schematic_notes:
  - 10k pull-down on Q1 gate
  - Ensures MOSFET Q1 is off when MCU T_RST_OUT is tristated
- designator: RN1
  type: resistor_array
  value: 33Ω
  footprint: RES-ARRAY-SMD_0402-8P-L2.0-W1.0-BL
  comment: 33Ω
  manufacturer: YAGEO(国巨)
  manufacturer_part: YC124-FR-0733RL
  supplier_part: C136851
  placement:
    x_mm: 30.432
    y_mm: 44.577
    rotation_deg: 0.0
    layer: T
  pins:
    '1': I2C1_SCL
    '2': QSPI1_IO0
    '3': QSPI1_SCK
    '4': QSPI1_IO3
    '5': QSPI_IO3
    '6': QSPI_SCK
    '7': QSPI_IO0
    '8': I2C1_SCL
  bom_data:
    No.: '43'
    Designator: RN1,RN2,RN3,RN4,RN5,RN6,RN7,RN8
    Quantity: '8'
    Manufacturer: YAGEO(国巨)
    Manufacturer Part: YC124-FR-0733RL
    Comment: 33Ω
    Footprint: RES-ARRAY-SMD_0402-8P-L2.0-W1.0-BL
    Mounting Style: SMT
    Supplier Part: C136851
    Datasheet: https://atta.szlcsc.com/upload/public/pdf/source/20180730/C256814_200CCA6CC84D78D7E49AE6680727F338.pdf
  schematic_page: P1
  function_block: QSPI and I2C series termination array
  schematic_notes:
  - 33 ohm 8-element array; terminates I2C1_SCL, QSPI1_IO0/3, QSPI_IO0/3, QSPI_SCK
- designator: RN2
  type: resistor_array
  value: 33Ω
  footprint: RES-ARRAY-SMD_0402-8P-L2.0-W1.0-BL
  comment: 33Ω
  manufacturer: YAGEO(国巨)
  manufacturer_part: YC124-FR-0733RL
  supplier_part: C136851
  placement:
    x_mm: 34.163
    y_mm: 45.212
    rotation_deg: 135.0
    layer: T
  pins:
    '1': GND
    '2': QSPI_IO2
    '3': QSPI_IO1
    '4': QSPI_CS
    '5': QSPI1_CS
    '6': QSPI1_IO1
    '7': QSPI1_IO2
    '8': GND
  bom_data:
    No.: '43'
    Designator: RN1,RN2,RN3,RN4,RN5,RN6,RN7,RN8
    Quantity: '8'
    Manufacturer: YAGEO(国巨)
    Manufacturer Part: YC124-FR-0733RL
    Comment: 33Ω
    Footprint: RES-ARRAY-SMD_0402-8P-L2.0-W1.0-BL
    Mounting Style: SMT
    Supplier Part: C136851
    Datasheet: https://atta.szlcsc.com/upload/public/pdf/source/20180730/C256814_200CCA6CC84D78D7E49AE6680727F338.pdf
  schematic_page: P1
  function_block: QSPI series termination array
  schematic_notes:
  - 33 ohm 8-element array; terminates QSPI_IO1/2/CS and QSPI1_IO1/2/CS
- designator: RN3
  type: resistor_array
  value: 33Ω
  footprint: RES-ARRAY-SMD_0402-8P-L2.0-W1.0-BL
  comment: 33Ω
  manufacturer: YAGEO(国巨)
  manufacturer_part: YC124-FR-0733RL
  supplier_part: C136851
  placement:
    x_mm: 37.338
    y_mm: 39.05
    rotation_deg: 90.0
    layer: T
  pins:
    '1': $1N200203
    '2': $1N200201
    '3': $1N200200
    '4': $1N200169
    '5': SD_CS
    '6': SPI2_MOSI
    '7': SPI2_CLK
    '8': FLASH_CS
  bom_data:
    No.: '43'
    Designator: RN1,RN2,RN3,RN4,RN5,RN6,RN7,RN8
    Quantity: '8'
    Manufacturer: YAGEO(国巨)
    Manufacturer Part: YC124-FR-0733RL
    Comment: 33Ω
    Footprint: RES-ARRAY-SMD_0402-8P-L2.0-W1.0-BL
    Mounting Style: SMT
    Supplier Part: C136851
    Datasheet: https://atta.szlcsc.com/upload/public/pdf/source/20180730/C256814_200CCA6CC84D78D7E49AE6680727F338.pdf
  schematic_page: P2
  function_block: SPI and SD card series termination array
  schematic_notes:
  - 33 ohm 8-element array; terminates SD_CS, SPI2_MOSI, SPI2_CLK, FLASH_CS
- designator: RN4
  type: resistor_array
  value: 33Ω
  footprint: RES-ARRAY-SMD_0402-8P-L2.0-W1.0-BL
  comment: 33Ω
  manufacturer: YAGEO(国巨)
  manufacturer_part: YC124-FR-0733RL
  supplier_part: C136851
  placement:
    x_mm: 24.257
    y_mm: 30.226
    rotation_deg: 315.0
    layer: T
  pins:
    '1': PA0
    '2': PA1
    '3': SERIAL_TXD
    '4': SERIAL_RXD
    '5': $3N4411
    '6': $3N4412
    '7': $3N4413
    '8': $3N4414
  bom_data:
    No.: '43'
    Designator: RN1,RN2,RN3,RN4,RN5,RN6,RN7,RN8
    Quantity: '8'
    Manufacturer: YAGEO(国巨)
    Manufacturer Part: YC124-FR-0733RL
    Comment: 33Ω
    Footprint: RES-ARRAY-SMD_0402-8P-L2.0-W1.0-BL
    Mounting Style: SMT
    Supplier Part: C136851
    Datasheet: https://atta.szlcsc.com/upload/public/pdf/source/20180730/C256814_200CCA6CC84D78D7E49AE6680727F338.pdf
  schematic_page: P3
  function_block: MCU GPIO and UART series termination array
  schematic_notes:
  - 33 ohm 8-element array; terminates PA0, PA1, SERIAL_TXD, SERIAL_RXD
- designator: RN5
  type: resistor_array
  value: 33Ω
  footprint: RES-ARRAY-SMD_0402-8P-L2.0-W1.0-BL
  comment: 33Ω
  manufacturer: YAGEO(国巨)
  manufacturer_part: YC124-FR-0733RL
  supplier_part: C136851
  placement:
    x_mm: 27.686
    y_mm: 30.861
    rotation_deg: 315.0
    layer: T
  pins:
    '1': PA4
    '2': PA5
    '3': PA6
    '4': PA7
    '5': $3N4403
    '6': $3N4404
    '7': $3N4405
    '8': $3N4406
  bom_data:
    No.: '43'
    Designator: RN1,RN2,RN3,RN4,RN5,RN6,RN7,RN8
    Quantity: '8'
    Manufacturer: YAGEO(国巨)
    Manufacturer Part: YC124-FR-0733RL
    Comment: 33Ω
    Footprint: RES-ARRAY-SMD_0402-8P-L2.0-W1.0-BL
    Mounting Style: SMT
    Supplier Part: C136851
    Datasheet: https://atta.szlcsc.com/upload/public/pdf/source/20180730/C256814_200CCA6CC84D78D7E49AE6680727F338.pdf
  schematic_page: P3
  function_block: MCU GPIO series termination array
  schematic_notes:
  - 33 ohm 8-element array; terminates PA4, PA5, PA6, PA7
- designator: RN6
  type: resistor_array
  value: 33Ω
  footprint: RES-ARRAY-SMD_0402-8P-L2.0-W1.0-BL
  comment: 33Ω
  manufacturer: YAGEO(国巨)
  manufacturer_part: YC124-FR-0733RL
  supplier_part: C136851
  placement:
    x_mm: 42.799
    y_mm: 24.13
    rotation_deg: 225.0
    layer: T
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
