koendv/arm_can_tool/applications/no_card.c

#include <stdint.h>
#include <romdisk.h>

/*
   This is a 32mbyte FAT32 disk image, containing a single file "NO_CARD.TXT".
   The file "NO_CARD.TXT" contains the text "insert card".
 */

#define ROMDISK_SECTOR_COUNT 65536 /* 32 MByte */

static const struct romdisk_sparse_sector no_card_sparse[] = {
    { 0, {
        0xeb, 0x58, 0x90, 0x6d, 0x6b, 0x66, 0x73, 0x2e, 0x66, 0x61, 0x74, 0x00, 0x02, 0x01, 0x20, 0x00,
        0x02, 0x00, 0x00, 0x00, 0x00, 0xf8, 0x00, 0x00, 0x20, 0x00, 0x04, 0x00, 0x00, 0x00, 0x00, 0x00,
        0x00, 0x00, 0x01, 0x00, 0xf8, 0x01, 0x00, 0x00, 0x00, 0x00, 0x00, 0x00, 0x02, 0x00, 0x00, 0x00,
        0x01, 0x00, 0x06, 0x00, 0x00, 0x00, 0x00, 0x00, 0x00, 0x00, 0x00, 0x00, 0x00, 0x00, 0x00, 0x00,
        0x80, 0x00, 0x29, 0x00, 0x00, 0x00, 0x00, 0x4e, 0x4f, 0x5f, 0x43, 0x41, 0x52, 0x44, 0x20, 0x20,
        0x20, 0x20, 0x46, 0x41, 0x54, 0x33, 0x32, 0x20, 0x20, 0x20, 0x0e, 0x1f, 0xbe, 0x77, 0x7c, 0xac,
        0x22, 0xc0, 0x74, 0x0b, 0x56, 0xb4, 0x0e, 0xbb, 0x07, 0x00, 0xcd, 0x10, 0x5e, 0xeb, 0xf0, 0x32,
        0xe4, 0xcd, 0x16, 0xcd, 0x19, 0xeb, 0xfe, 0x54, 0x68, 0x69, 0x73, 0x20, 0x69, 0x73, 0x20, 0x6e,
        0x6f, 0x74, 0x20, 0x61, 0x20, 0x62, 0x6f, 0x6f, 0x74, 0x61, 0x62, 0x6c, 0x65, 0x20, 0x64, 0x69,
        0x73, 0x6b, 0x2e, 0x20, 0x20, 0x50, 0x6c, 0x65, 0x61, 0x73, 0x65, 0x20, 0x69, 0x6e, 0x73, 0x65,
        0x72, 0x74, 0x20, 0x61, 0x20, 0x62, 0x6f, 0x6f, 0x74, 0x61, 0x62, 0x6c, 0x65, 0x20, 0x66, 0x6c,
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
        0x00, 0x00, 0x00, 0x00, 0x00, 0x00, 0x00, 0x00, 0x00, 0x00, 0x00, 0x00, 0x00, 0x00, 0x00, 0x00,
        0x00, 0x00, 0x00, 0x00, 0x00, 0x00, 0x00, 0x00, 0x00, 0x00, 0x00, 0x00, 0x00, 0x00, 0x00, 0x00,
        0x00, 0x00, 0x00, 0x00, 0x00, 0x00, 0x00, 0x00, 0x00, 0x00, 0x00, 0x00, 0x00, 0x00, 0x00, 0x00,
        0x00, 0x00, 0x00, 0x00, 0x00, 0x00, 0x00, 0x00, 0x00, 0x00, 0x00, 0x00, 0x00, 0x00, 0x00, 0x00,
        0x00, 0x00, 0x00, 0x00, 0x00, 0x00, 0x00, 0x00, 0x00, 0x00, 0x00, 0x00, 0x00, 0x00, 0x00, 0x00,
        0x00, 0x00, 0x00, 0x00, 0x00, 0x00, 0x00, 0x00, 0x00, 0x00, 0x00, 0x00, 0x00, 0x00, 0x00, 0x00,
        0x00, 0x00, 0x00, 0x00, 0x00, 0x00, 0x00, 0x00, 0x00, 0x00, 0x00, 0x00, 0x00, 0x00, 0x00, 0x00,
        0x00, 0x00, 0x00, 0x00, 0x00, 0x00, 0x00, 0x00, 0x00, 0x00, 0x00, 0x00, 0x00, 0x00, 0x00, 0x00,
        0x00, 0x00, 0x00, 0x00, 0x00, 0x00, 0x00, 0x00, 0x00, 0x00, 0x00, 0x00, 0x00, 0x00, 0x00, 0x00,
    } },
};

ROMDISK_IMAGE(no_card, no_card_sparse, ROMDISK_SECTOR_COUNT);

/* not truncated */
