koendv/arm_can_tool/applications/sdcard.c

#include <rtdevice.h>
#define DBG_TAG "SD"
#define DBG_LVL DBG_INFO
#include <rtdbg.h>

#include <drv_spi.h>
#include <dev_spi_msd.h>
#include <dfs_fs.h>
#include <stdbool.h>
#include "board.h"
#include "pins.h"
#include "settings.h"
#include "ulog_file.h"
#include "sdcard.h"

#define SD_DEVICE         "sd0"
#define SD_DIR            "/sdcard"
#define SD_SPI_BUS        "spi2"
#define SD_SPI_DEV        "spi21"
#define SD0_CS_GPIO       GPIOA
#define SD0_CS_GPIO_PIN   GPIO_PINS_11
#define SD_DEBOUNCE_TICKS (RT_TICK_PER_SECOND / 10)
#define SD_BIG_STACK      (5 * 1024)

bool              sdcard_mounted    = false;
static rt_timer_t sdcard_change_tim = RT_NULL;

/*
 The process of inserting an SD card in a running system is:

- an SD card is inserted
- the SD_DETECT signal goes low
- the processor is interrupted
- software switches the load switch on
- wait 10ms for the SD card to power up
- software asserts SD card chip select
- wait 10ms
- software mounts the card filesystem

 */

static void sdcard_mount(void *param)
{
    (void)param;
    rt_err_t err;
    bool     sd_detect = FALSE;

    sd_detect = rt_pin_read(SD_DETECT_PIN) == PIN_LOW;
    if (sd_detect)
    {
        if (sdcard_mounted)
            return;

        LOG_D("sdcard mount");

        rt_pin_write(SD_CS_PIN, PIN_HIGH); // sdcard chip select off
        rt_thread_mdelay(10);
        rt_pin_write(SD_ON_PIN, PIN_HIGH); // sdcard power on
        rt_thread_mdelay(10);
        rt_pin_write(SD_CS_PIN, PIN_LOW);  // sdcard chip select on
        rt_thread_mdelay(10);

        err = rt_hw_spi_device_attach(SD_SPI_BUS, SD_SPI_DEV, SD0_CS_GPIO, SD0_CS_GPIO_PIN);
        if (err != RT_EOK)
        {
            LOG_E("spi attach fail");
            return;
        }

        err = msd_init(SD_DEVICE, SD_SPI_DEV);
        if (err != RT_EOK)
        {
            LOG_E("sd card msd init fail");
            return;
        }

        if (settings.mode != MODE_MASS_STORAGE)
        {
            err = dfs_mount(SD_DEVICE, SD_DIR, "elm", 0, 0);
            if (err != RT_EOK)
            {
                LOG_E("sd card mount fail");
                return;
            }
        }

        sdcard_mounted = true;

        LOG_I("sd card mount to " SD_DIR);
    }
    else
    {
        if (sdcard_mounted)
        {
            LOG_I("sdcard unmount");

            if (settings.mode != MODE_MASS_STORAGE)
            {
                dfs_unmount(SD_DIR);           // unmount
            }
            rt_pin_write(SD_CS_PIN, PIN_HIGH); // sdcard chip select off
            rt_thread_mdelay(10);
            rt_pin_write(SD_ON_PIN, PIN_LOW);  // sdcard power off
            sdcard_mounted = false;
        }
    }

    return;
}

/* thread called when debounce timer expires */
static void sdcard_change_thread(void *parameter)
{
    rt_thread_t threadid = RT_NULL;

    // mounting the sdcard requires a lot of stack,
    // so we start up a separate thread with a big stack.
    // increase stack if mounting sdcard crashes.

    threadid = rt_thread_create("sd mount", sdcard_mount, RT_NULL, SD_BIG_STACK, 5, 10);
    if (threadid != RT_NULL)
        rt_thread_startup(threadid);

    rt_timer_stop(sdcard_change_tim);
}

/* interrupt handler */
static void sdcard_change_handler(void *ptr)
{
    if (sdcard_change_tim != RT_NULL)
        rt_timer_start(sdcard_change_tim);
}

int sdcard_init(void)
{
    rt_pin_mode(SD_CS_PIN, PIN_MODE_OUTPUT);
    rt_pin_write(SD_CS_PIN, PIN_HIGH);

    rt_pin_mode(SD_ON_PIN, PIN_MODE_OUTPUT);
    rt_pin_write(SD_ON_PIN, PIN_LOW);

    rt_pin_mode(SD_DETECT_PIN, PIN_MODE_INPUT_PULLUP);

    sdcard_change_tim = rt_timer_create("sdcard",
                                        sdcard_change_thread,
                                        RT_NULL,
                                        SD_DEBOUNCE_TICKS,
                                        RT_TIMER_FLAG_ONE_SHOT | RT_TIMER_FLAG_SOFT_TIMER);

    rt_pin_attach_irq(SD_DETECT_PIN, PIN_IRQ_MODE_RISING_FALLING, sdcard_change_handler, RT_NULL);
    rt_pin_irq_enable(SD_DETECT_PIN, PIN_IRQ_ENABLE);

    sdcard_mount(RT_NULL);

    return RT_EOK;
}
